DarkCaster/3DPrintingStuff/GearedExtruderDrive_V2/DriveIdler_Top/DriveIdler_Cover_625zz.FCStd

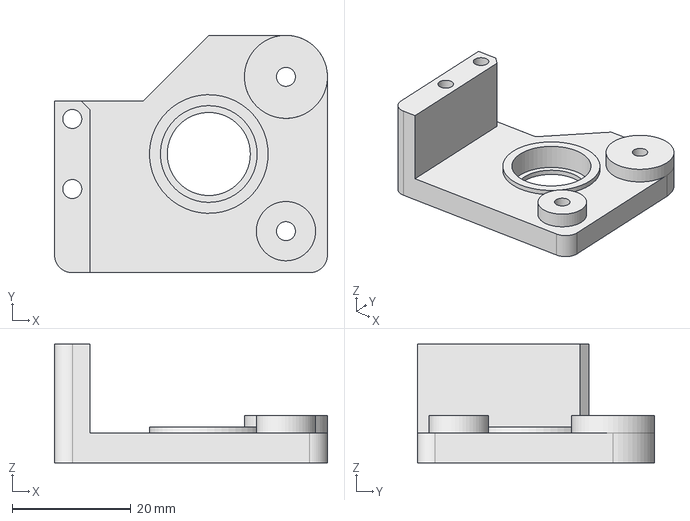
[picture p15: CAD file, 2019-01-30]
GearedExtruderDrive_V2/DriveIdler_Top/DriveIdler_Cover_625zz.FCStd
46.0 x 40.0 x 20.0 mm
