DarkCaster/3DPrintingStuff/GearedExtruderDrive_V2/Frame/FrameTop.FCStd

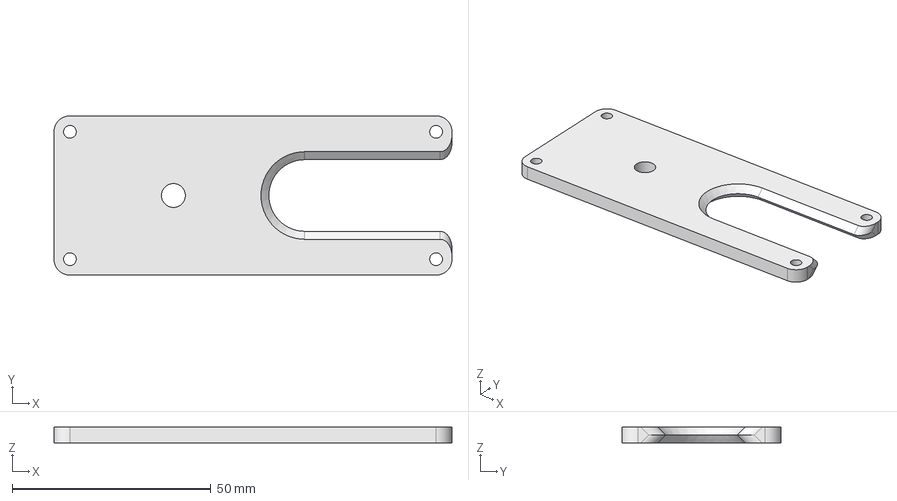
[picture p16: CAD file, 2019-02-06]
GearedExtruderDrive_V2/Frame/FrameTop.FCStd
100.0 x 40.0 x 4.00 mm
