DarkCaster/3DPrintingStuff/GearedExtruderDrive_V2/Helpers/Nema17_Motor.FCStd

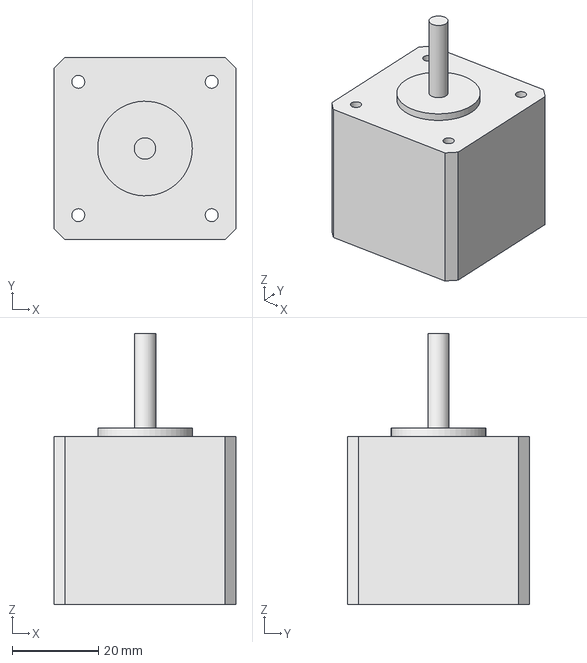
[picture p17: CAD file, 2019-01-29]
GearedExtruderDrive_V2/Helpers/Nema17_Motor.FCStd
42.3 x 42.3 x 63.0 mm
