DarkCaster/3DPrintingStuff/GearedExtruderDrive_V2/SmallGear/SmallGear_D5.4mm+M2.5.FCStd

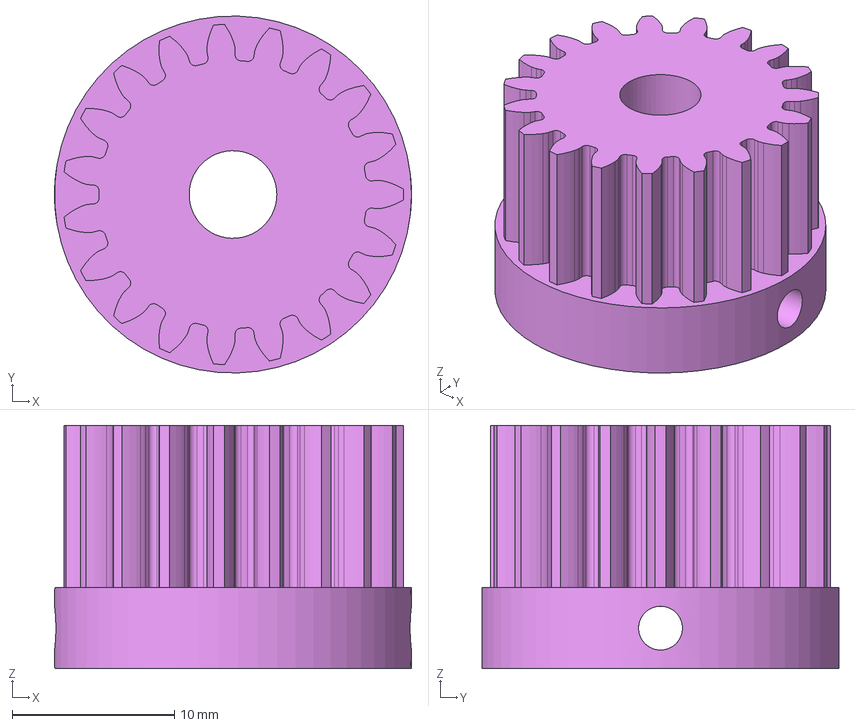
[picture p19: CAD file, 2018-07-12]
GearedExtruderDrive_V2/SmallGear/SmallGear_D5.4mm+M2.5.FCStd
22.0 x 22.0 x 15.0 mm
