DarkCaster/3DPrintingStuff/OPIRouterCase4/Bottom_Extension_Model.FCStd

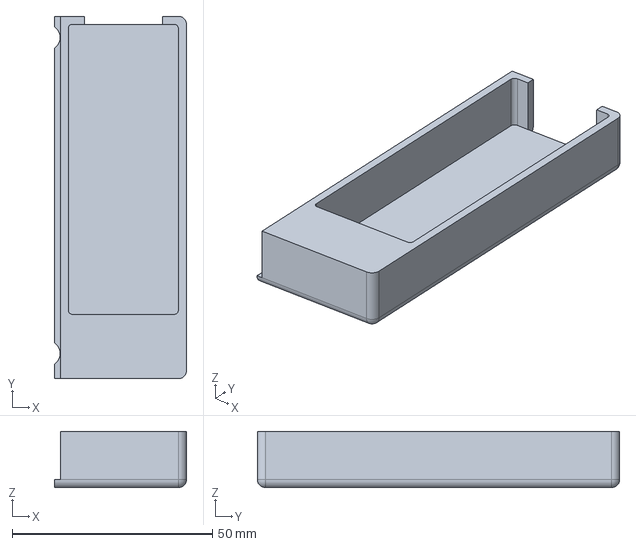
[picture p21: CAD file, 2024-11-16]
OPIRouterCase4/Bottom_Extension_Model.FCStd
33.0 x 90.6 x 14.0 mm
