DarkCaster/3DPrintingStuff/Other/StuffOrganizerV1.FCStd

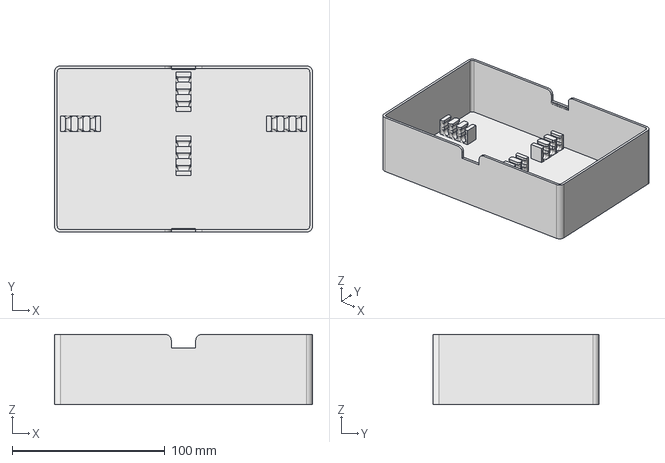
[picture p22: CAD file, 2023-09-04]
Other/StuffOrganizerV1.FCStd
169.0 x 109.0 x 46.0 mm
