DarkCaster/3DPrintingStuff/RepRap_Huxley_CustomParts/ExtruderDriveHolder/ExtruderDriveHolder4_NEMA17_Alt.FCStd

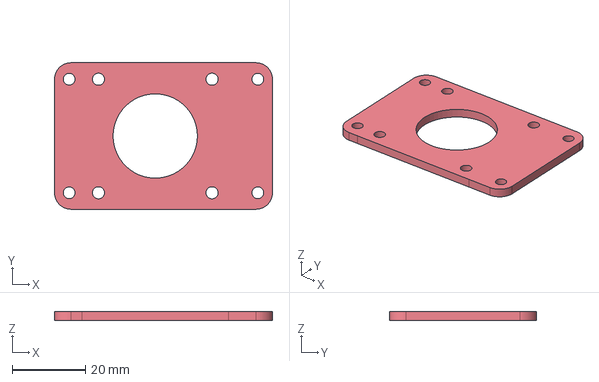
[picture p23: CAD file, 2018-10-10]
RepRap_Huxley_CustomParts/ExtruderDriveHolder/ExtruderDriveHolder4_NEMA17_Alt.FCStd
59.5 x 40.0 x 2.50 mm
