DarkCaster/3DPrintingStuff/RepRap_Huxley_CustomParts/Helpers/OpticalEndstop.FCStd

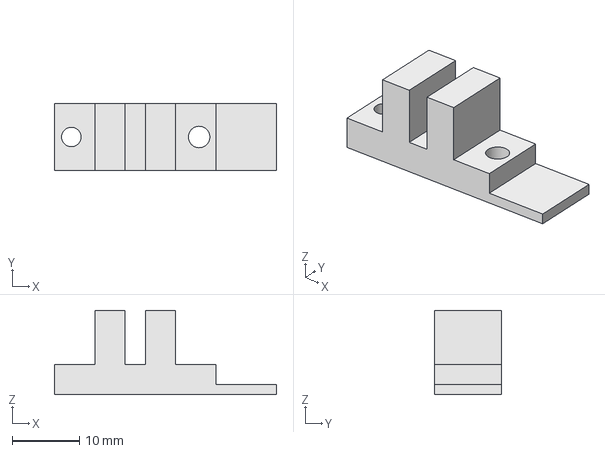
[picture p24: CAD file, 2019-01-16]
RepRap_Huxley_CustomParts/Helpers/OpticalEndstop.FCStd
33.0 x 10.0 x 12.5 mm
