DarkCaster/3DPrintingStuff/RepRap_Huxley_CustomParts/Other/LM6UU_IGUS_PETG.fcstd

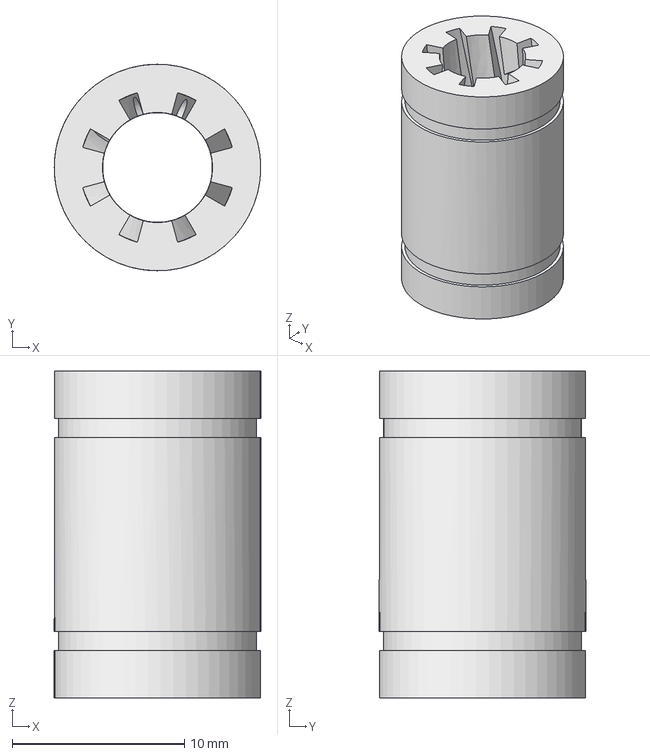
[picture p25: CAD file, 2019-02-09]
RepRap_Huxley_CustomParts/Other/LM6UU_IGUS_PETG.fcstd
12.0 x 12.0 x 19.0 mm
