DarkCaster/3DPrintingStuff/RepRap_Huxley_CustomParts/XAxis_Left/LeftXEndHalf_Top.FCStd

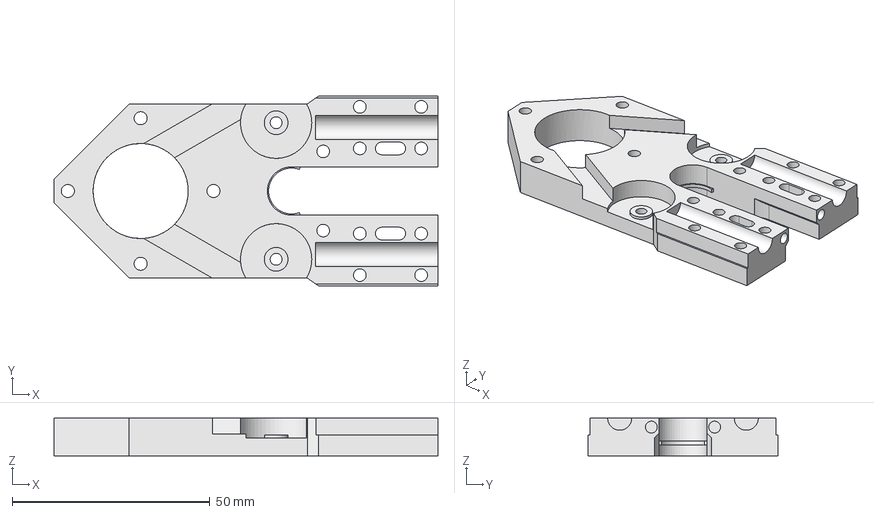
[picture p26: CAD file, 2019-01-19]
RepRap_Huxley_CustomParts/XAxis_Left/LeftXEndHalf_Top.FCStd
97.0 x 48.0 x 9.50 mm
