DarkCaster/3DPrintingStuff/RepRap_Huxley_CustomParts/XCarriage/BackTurbinePipe_TwoSides.FCStd

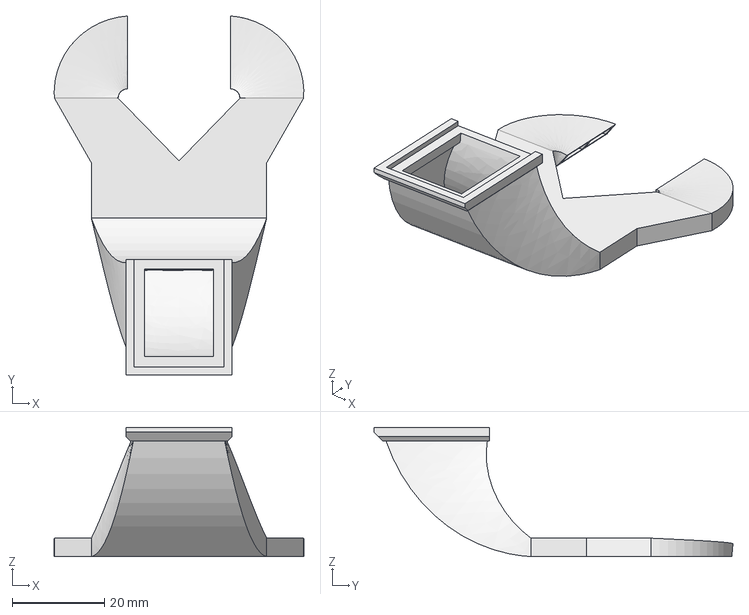
[picture p28: CAD file, 2019-01-26]
RepRap_Huxley_CustomParts/XCarriage/BackTurbinePipe_TwoSides.FCStd
54.1 x 77.8 x 28.0 mm
