DarkCaster/3DPrintingStuff/RepRap_Huxley_CustomParts/YAxis/BedClamping1_Alt2.FCStd

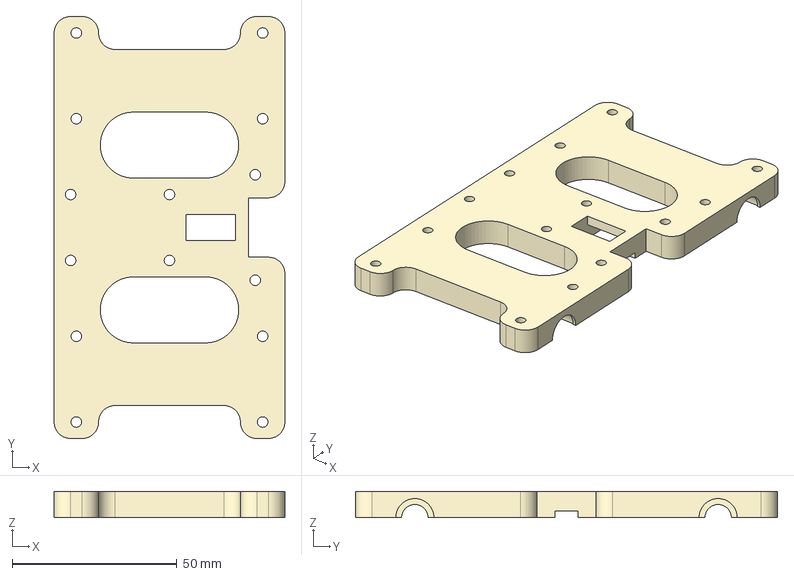
[picture p29: CAD file, 2018-10-08]
RepRap_Huxley_CustomParts/YAxis/BedClamping1_Alt2.FCStd
70.0 x 128.0 x 8.00 mm
