DarkCaster/3DPrintingStuff/RepRap_Huxley_CustomParts/ZAxis/ZThreadedRodCoupler_THSL-200-8D_D8mm.FCStd

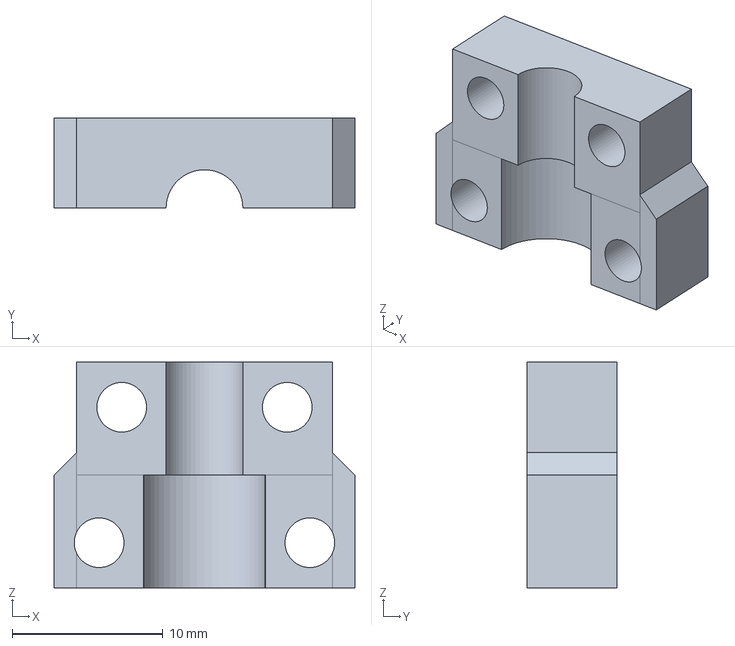
[picture p30: CAD file, 2018-09-16]
RepRap_Huxley_CustomParts/ZAxis/ZThreadedRodCoupler_THSL-200-8D_D8mm.FCStd
20.0 x 6.00 x 15.0 mm
