DarkCaster/3DPrintingStuff/Anet_E10_X_BeltLock/RightBeltLock.FCStd

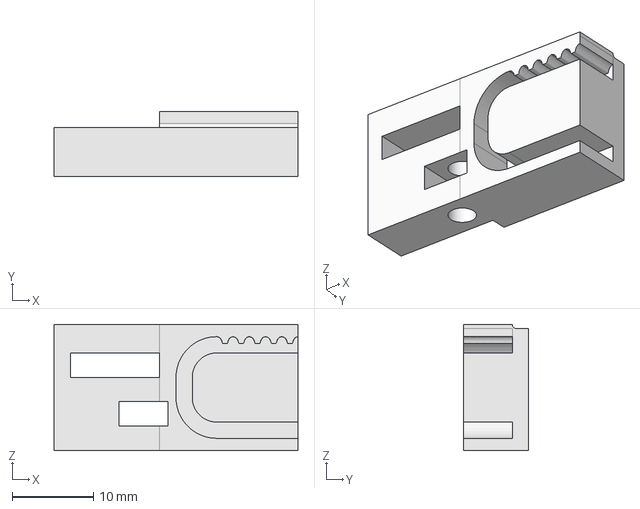
[picture p31: CAD file, 2018-05-15]
Anet_E10_X_BeltLock/RightBeltLock.FCStd
30.0 x 8.00 x 15.5 mm
