DarkCaster/3DPrintingStuff/Anet_E10_X_Carriage/XCarriage.fcstd

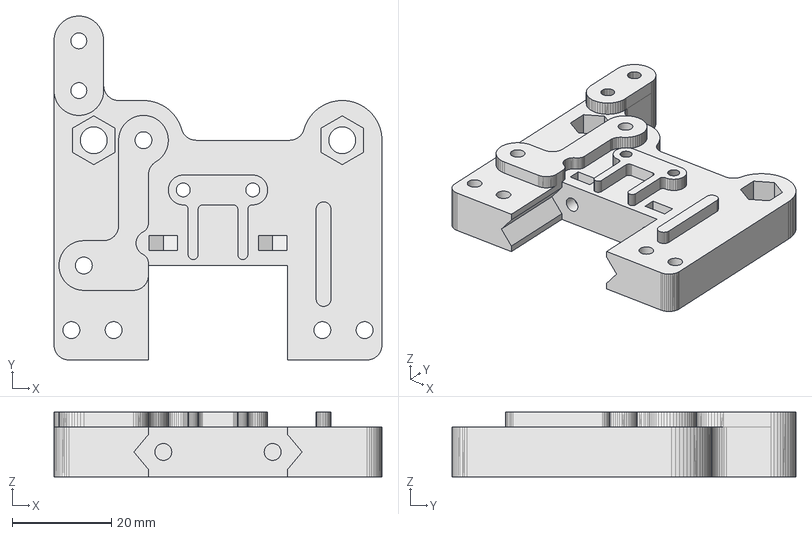
[picture p32: CAD file, 2018-11-25]
Anet_E10_X_Carriage/XCarriage.fcstd
66.0 x 69.2 x 13.0 mm
