DarkCaster/3DPrintingStuff/CalibrationSquare/VerticalSquare_Fusion.FCStd

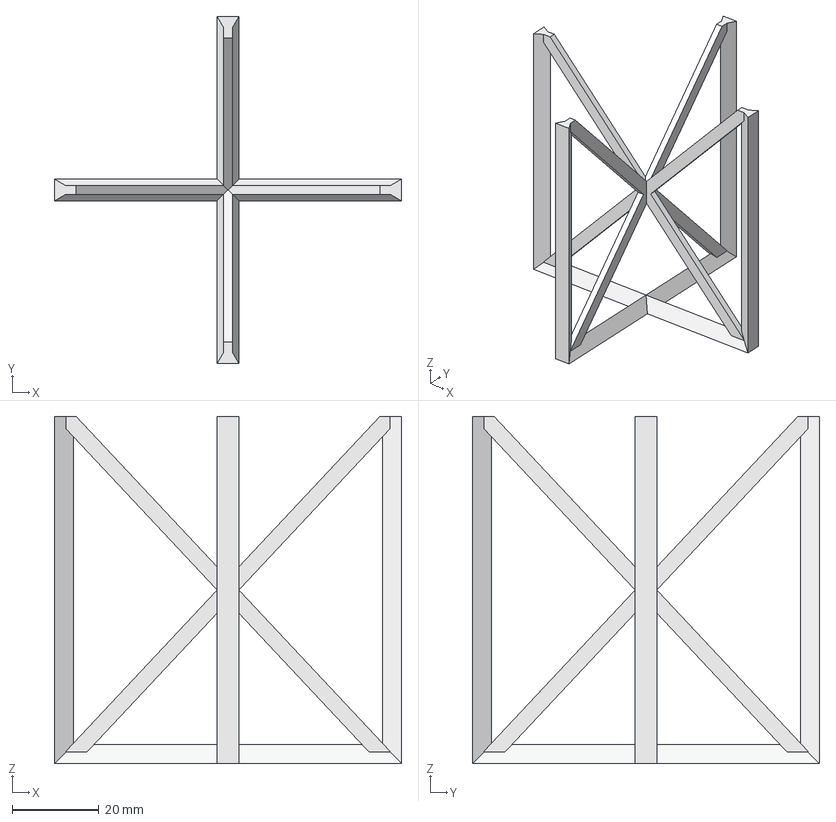
[picture p33: CAD file, 2018-10-27]
CalibrationSquare/VerticalSquare_Fusion.FCStd
80.0 x 80.0 x 80.0 mm
