DarkCaster/3DPrintingStuff/FilamentFilter/Box.FCStd

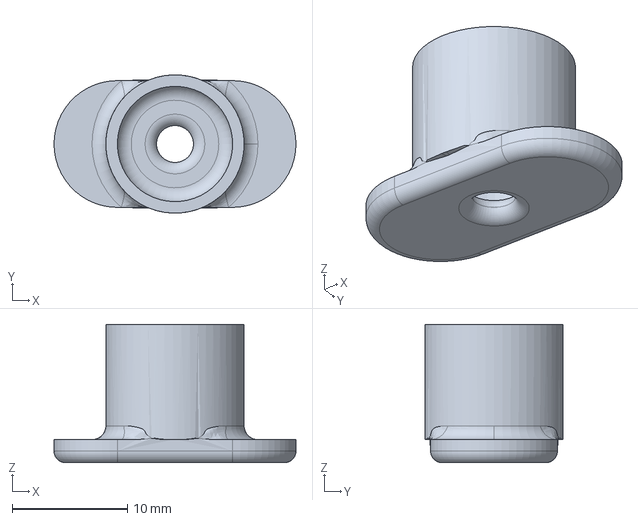
[picture p34: CAD file, 2018-07-15]
FilamentFilter/Box.FCStd
21.0 x 12.0 x 12.0 mm
