DarkCaster/3DPrintingStuff/GearedExtruderDrive_V1_NEMA17/SmallGear_V2_ABS_D5.2mm+M3.FCStd

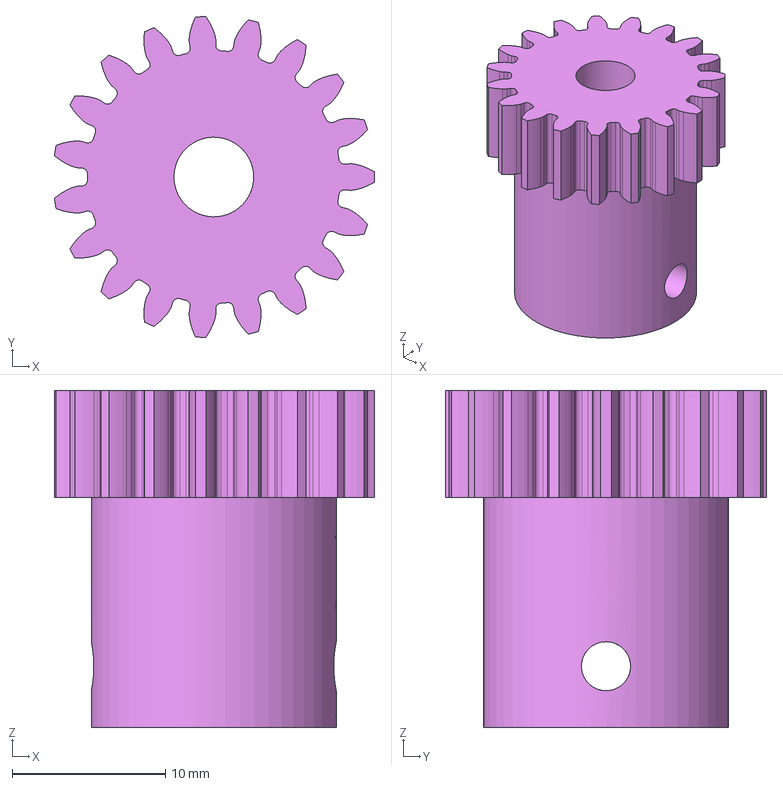
[picture p35: CAD file, 2018-07-07]
GearedExtruderDrive_V1_NEMA17/SmallGear_V2_ABS_D5.2mm+M3.FCStd
20.9 x 21.0 x 22.0 mm
