DarkCaster/3DPrintingStuff/GearedExtruderDrive_V2/DriveBase/DriveBase_Fitting_Clamp.FCStd

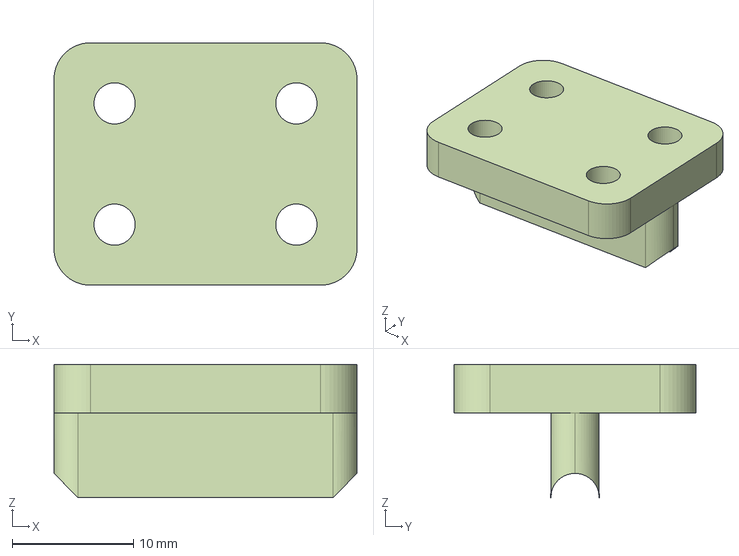
[picture p36: CAD file, 2019-02-08]
GearedExtruderDrive_V2/DriveBase/DriveBase_Fitting_Clamp.FCStd
25.0 x 20.0 x 11.0 mm
