DarkCaster/3DPrintingStuff/GearedExtruderDrive_V2/DriveIdler/DriveIdler_623zz.FCStd

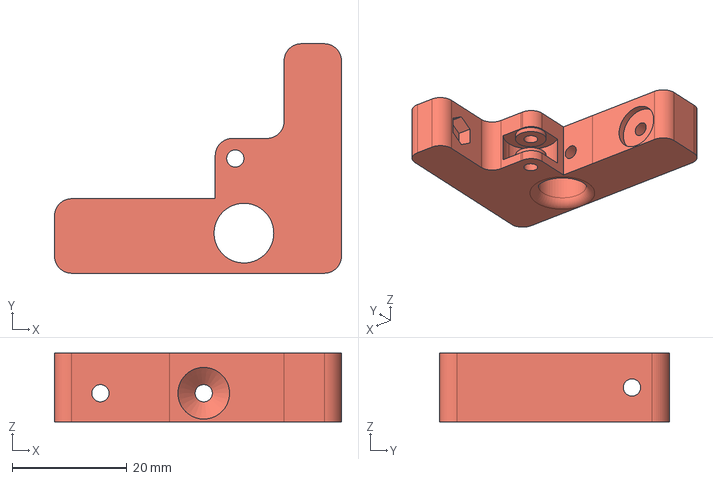
[picture p37: CAD file, 2018-07-15]
GearedExtruderDrive_V2/DriveIdler/DriveIdler_623zz.FCStd
50.0 x 40.0 x 12.0 mm
