DarkCaster/3DPrintingStuff/GearedExtruderDrive_V2/DriveIdler_Top/DriveIdlerClamp.FCStd

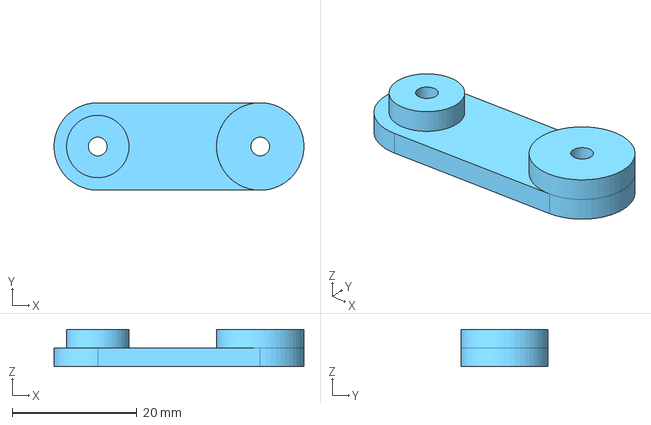
[picture p38: CAD file, 2018-07-15]
GearedExtruderDrive_V2/DriveIdler_Top/DriveIdlerClamp.FCStd
40.0 x 14.0 x 6.00 mm
