DarkCaster/3DPrintingStuff/GearedExtruderDrive_V2/LargeGearAssembly/LargeGear_M5_H8mm_ClipH4.6mm.FCStd

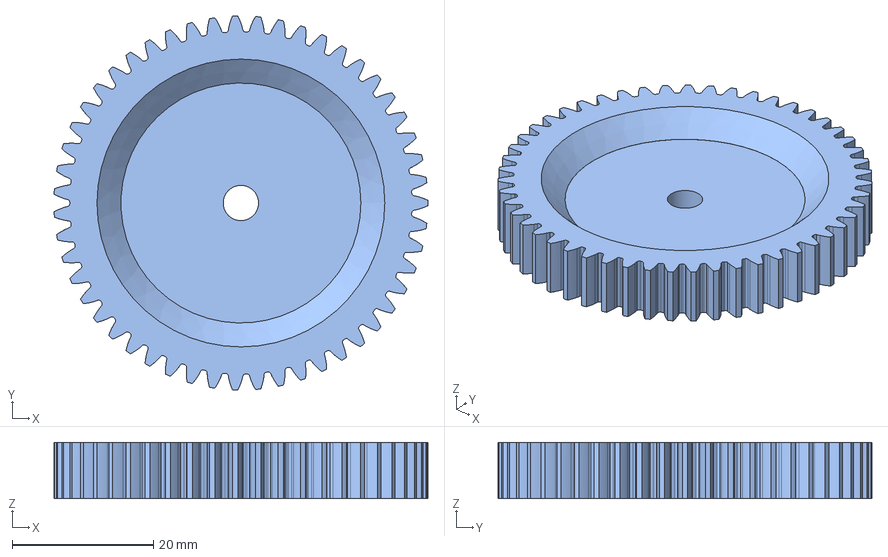
[picture p40: CAD file, 2019-02-07]
GearedExtruderDrive_V2/LargeGearAssembly/LargeGear_M5_H8mm_ClipH4.6mm.FCStd
53.0 x 53.0 x 8.00 mm
