DarkCaster/3DPrintingStuff/MiniSpool/MiniSpoolHalf2_Thick_30MM.fcstd

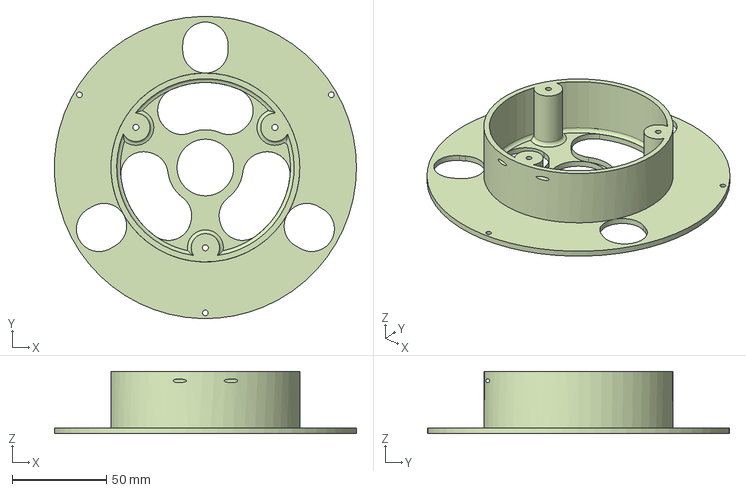
[picture p41: CAD file, 2018-12-30]
MiniSpool/MiniSpoolHalf2_Thick_30MM.fcstd
159.9 x 159.9 x 33.0 mm
