DarkCaster/3DPrintingStuff/OPIRouterCase4/Top_Case_Imported.FCStd

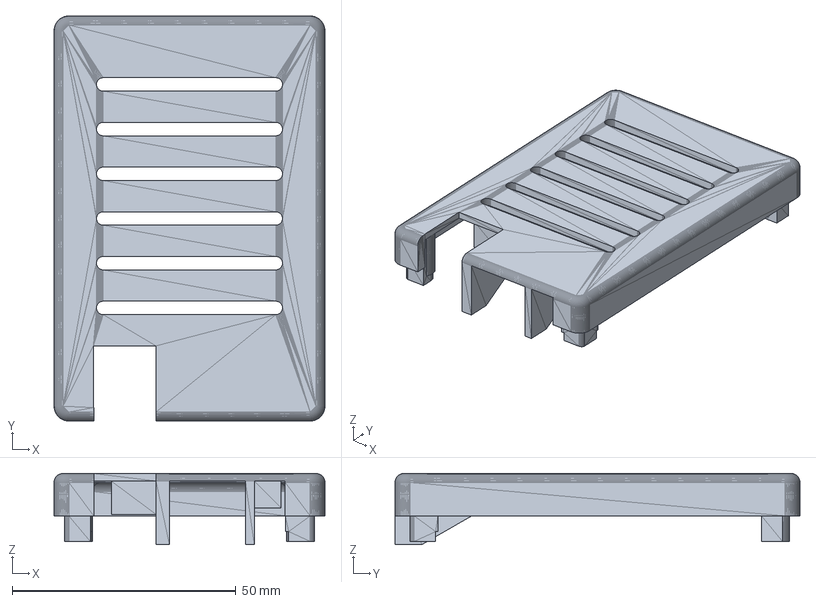
[picture p42: CAD file, 2024-11-16]
OPIRouterCase4/Top_Case_Imported.FCStd
60.6 x 90.6 x 15.9 mm
