DarkCaster/3DPrintingStuff/Other/CasePart1L.FCStd

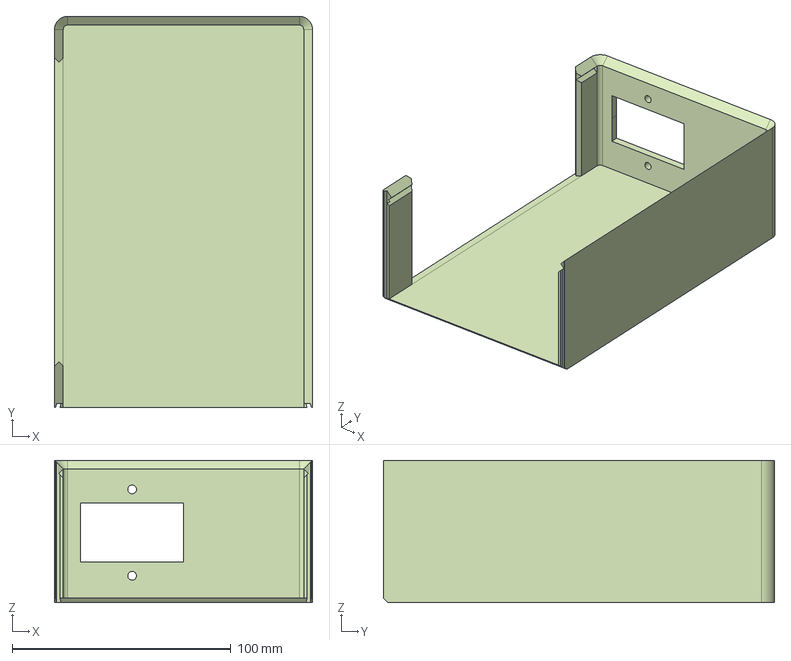
[picture p43: CAD file, 2019-06-28]
Other/CasePart1L.FCStd
118.0 x 179.0 x 65.0 mm
