DarkCaster/3DPrintingStuff/RepRap_Huxley_CustomParts/ExtruderDriveHolder/ExtruderDriveHolder1_Alt.FCStd

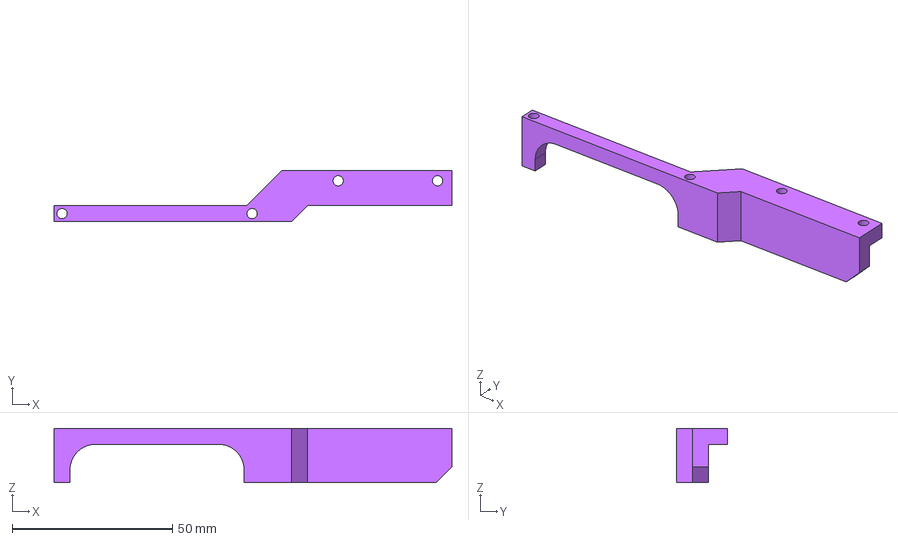
[picture p45: CAD file, 2018-10-10]
RepRap_Huxley_CustomParts/ExtruderDriveHolder/ExtruderDriveHolder1_Alt.FCStd
124.2 x 16.0 x 17.0 mm
