DarkCaster/3DPrintingStuff/RepRap_Huxley_CustomParts/Helpers/Rod_M6x365mm.FCStd

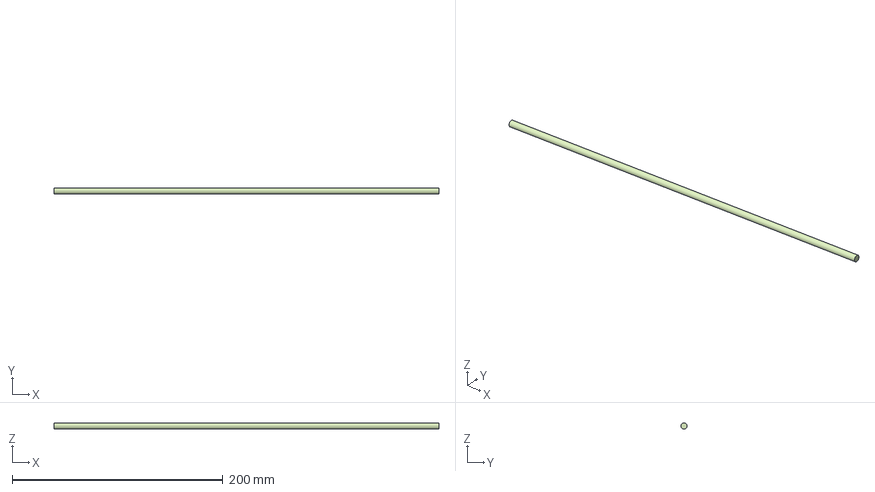
[picture p46: CAD file, 2019-01-15]
RepRap_Huxley_CustomParts/Helpers/Rod_M6x365mm.FCStd
365.0 x 5.99 x 6.00 mm
