DarkCaster/3DPrintingStuff/RepRap_Huxley_CustomParts/XAxis_Right/RightXEndHalf_Top.FCStd

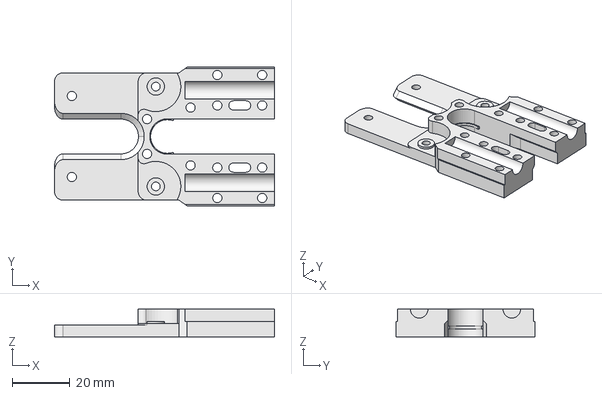
[picture p47: CAD file, 2019-01-19]
RepRap_Huxley_CustomParts/XAxis_Right/RightXEndHalf_Top.FCStd
76.0 x 48.0 x 9.50 mm
