DarkCaster/3DPrintingStuff/RepRap_Huxley_CustomParts/XCarriage/CarriageHalf_Top.FCStd

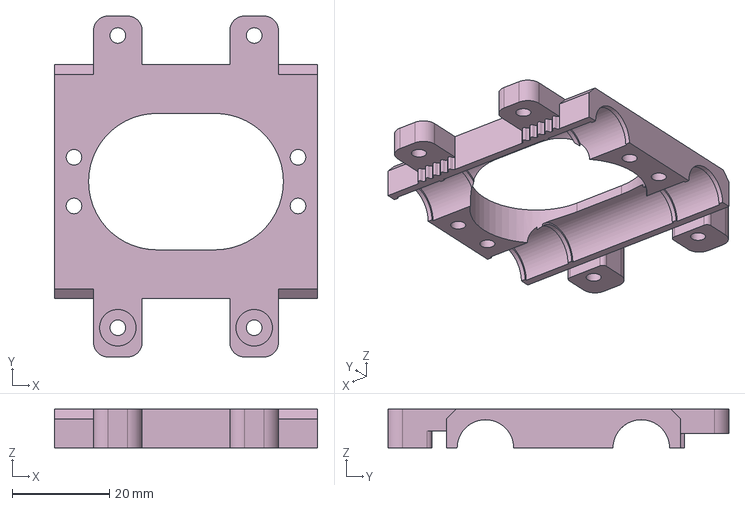
[picture p48: CAD file, 2019-01-17]
RepRap_Huxley_CustomParts/XCarriage/CarriageHalf_Top.FCStd
54.0 x 70.0 x 8.00 mm
