DarkCaster/3DPrintingStuff/RepRap_Huxley_CustomParts/YAxis/BedClamping2_Alt2.FCStd

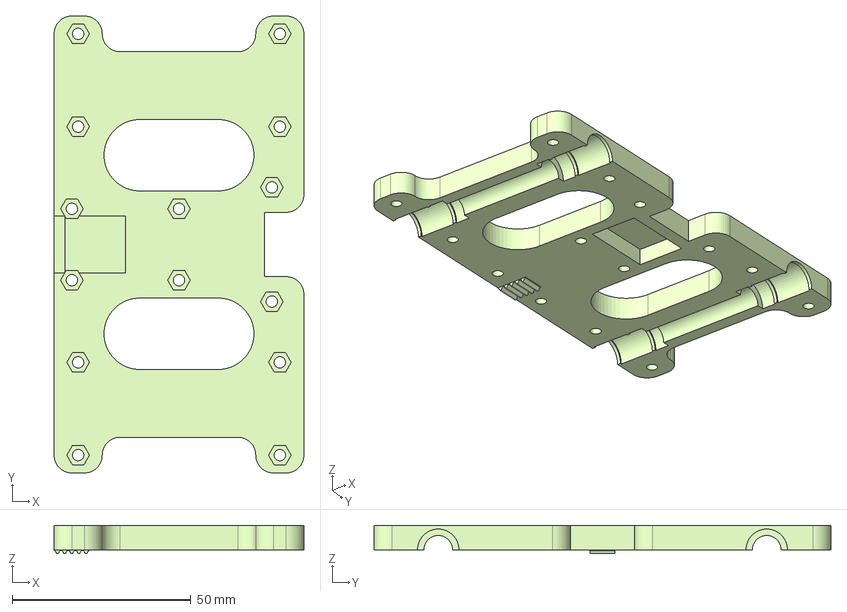
[picture p49: CAD file, 2018-10-08]
RepRap_Huxley_CustomParts/YAxis/BedClamping2_Alt2.FCStd
70.0 x 128.0 x 7.85 mm
