DarkCaster/3DPrintingStuff/RepRap_Huxley_CustomParts/ZAxis/ZThreadedRodCoupler_M5.FCStd

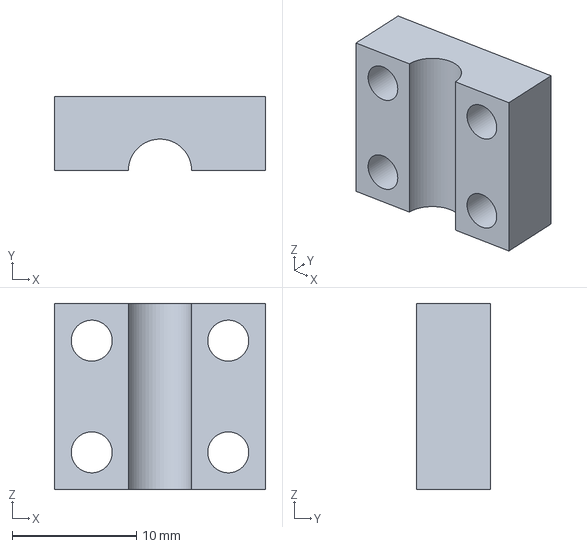
[picture p50: CAD file, 2018-09-03]
RepRap_Huxley_CustomParts/ZAxis/ZThreadedRodCoupler_M5.FCStd
17.0 x 6.00 x 15.0 mm
