DarkCaster/3DPrintingStuff/CalibrationSquare/VerticalSquare.FCStd

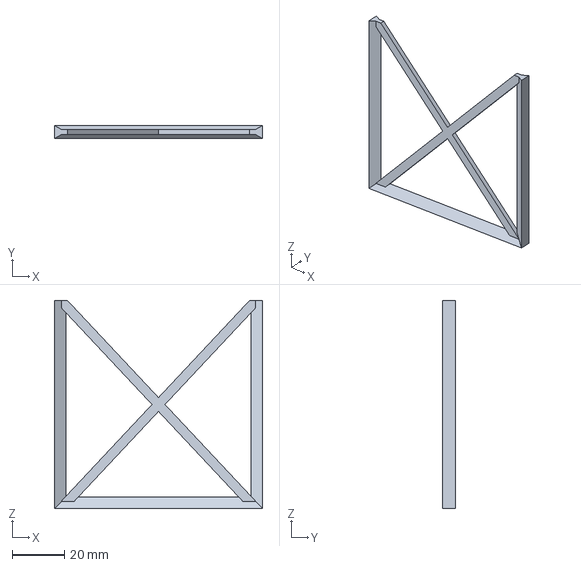
[picture p51: CAD file, 2018-07-15]
CalibrationSquare/VerticalSquare.FCStd
80.0 x 5.00 x 80.0 mm
