DarkCaster/3DPrintingStuff/GearedExtruderDrive_V2/DriveBase/DriveBase_Tight.FCStd

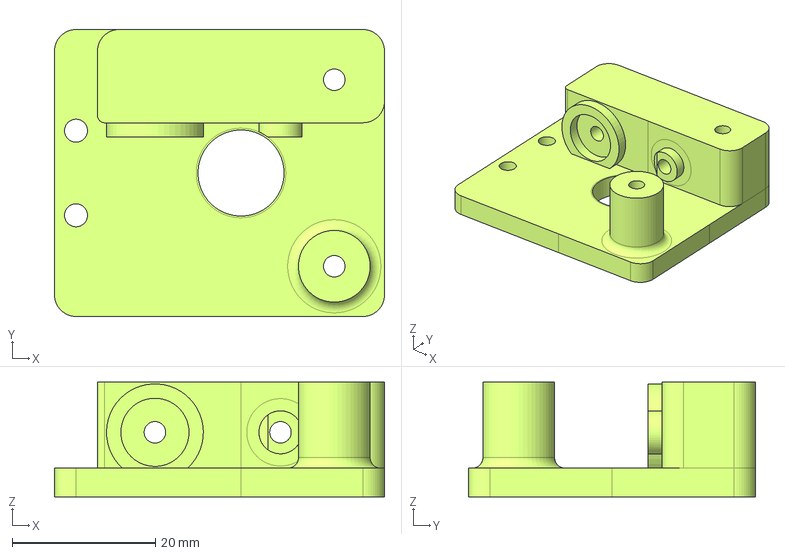
[picture p52: CAD file, 2018-10-31]
GearedExtruderDrive_V2/DriveBase/DriveBase_Tight.FCStd
46.0 x 40.0 x 16.0 mm
