DarkCaster/3DPrintingStuff/GearedExtruderDrive_V2/Frame/FrontStand_H20.5mm.FCStd

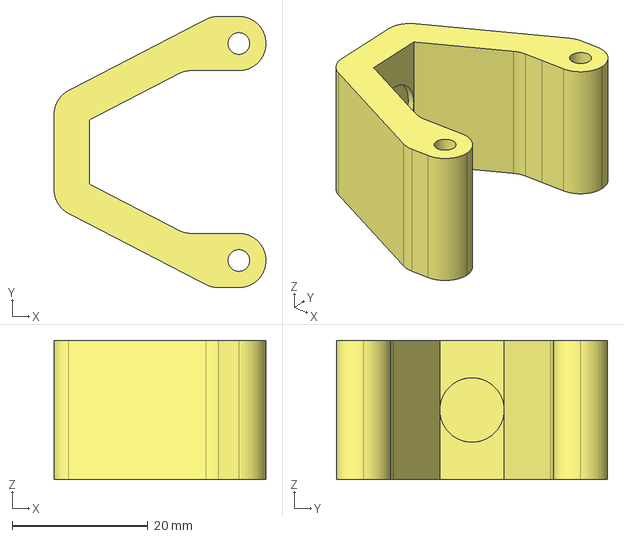
[picture p53: CAD file, 2018-07-12]
GearedExtruderDrive_V2/Frame/FrontStand_H20.5mm.FCStd
31.3 x 40.0 x 20.5 mm
