DarkCaster/3DPrintingStuff/GearedExtruderDrive_V2/LargeGearAssembly/IdlerPart_625zz.FCStd

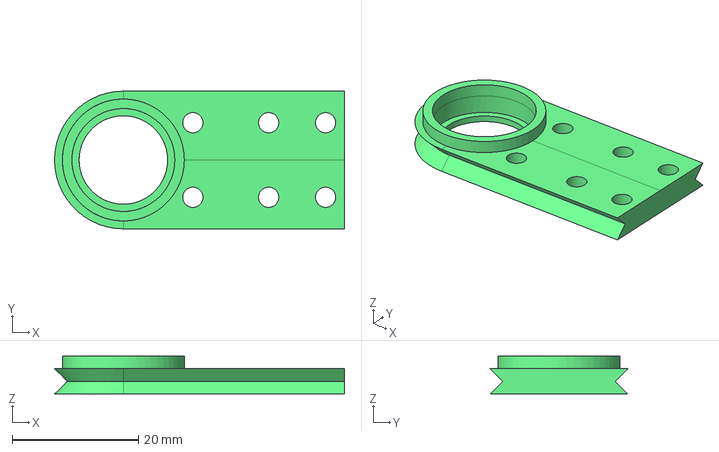
[picture p54: CAD file, 2018-07-12]
GearedExtruderDrive_V2/LargeGearAssembly/IdlerPart_625zz.FCStd
45.9 x 21.8 x 6.00 mm
