DarkCaster/3DPrintingStuff/MiniSpool/MiniSpoolHalf_Thick_15MM.fcstd

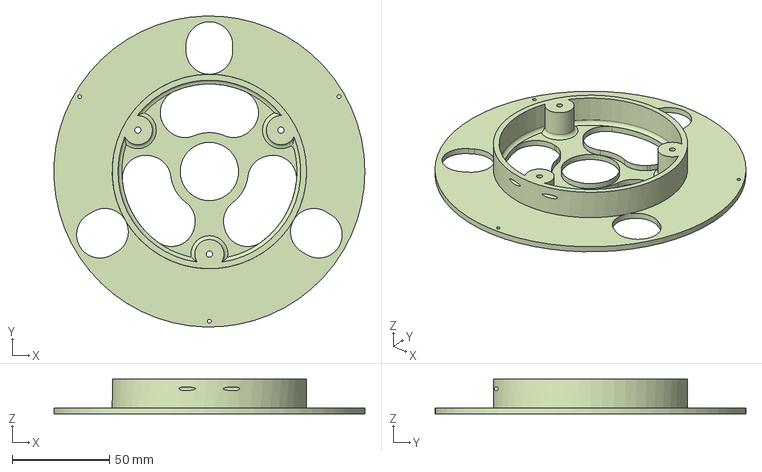
[picture p55: CAD file, 2018-11-22]
MiniSpool/MiniSpoolHalf_Thick_15MM.fcstd
159.9 x 159.9 x 18.0 mm
