DarkCaster/3DPrintingStuff/OPIRouterCase4/Bottom_Case_Imported.FCStd

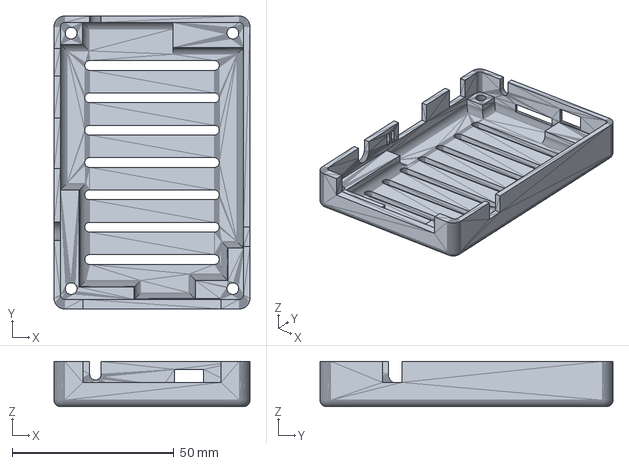
[picture p56: CAD file, 2024-11-16]
OPIRouterCase4/Bottom_Case_Imported.FCStd
60.6 x 90.6 x 14.0 mm
