DarkCaster/3DPrintingStuff/Other/ZTEBatteryPowerAdapter.fcstd

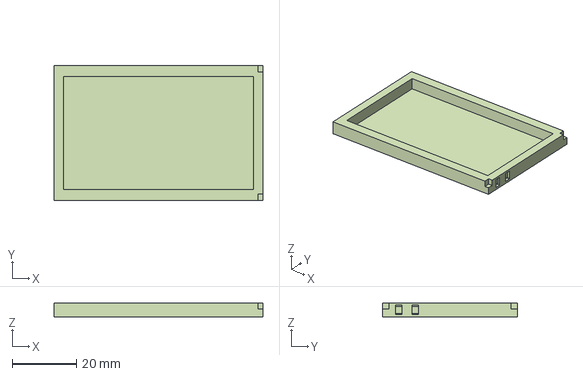
[picture p57: CAD file, 2018-11-06]
Other/ZTEBatteryPowerAdapter.fcstd
65.0 x 42.0 x 4.50 mm
