DarkCaster/3DPrintingStuff/RepRap_Huxley_CustomParts/BedRodsAlignmentToolHalf.FCStd

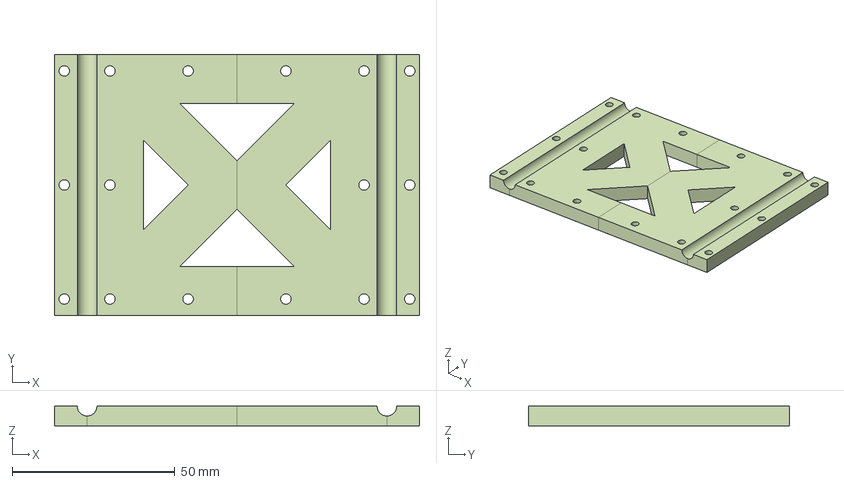
[picture p58: CAD file, 2018-10-02]
RepRap_Huxley_CustomParts/BedRodsAlignmentToolHalf.FCStd
112.0 x 80.0 x 6.00 mm
