DarkCaster/3DPrintingStuff/RepRap_Huxley_CustomParts/ExtruderDriveHolder/ExtruderDriveHolder_Clip.FCStd

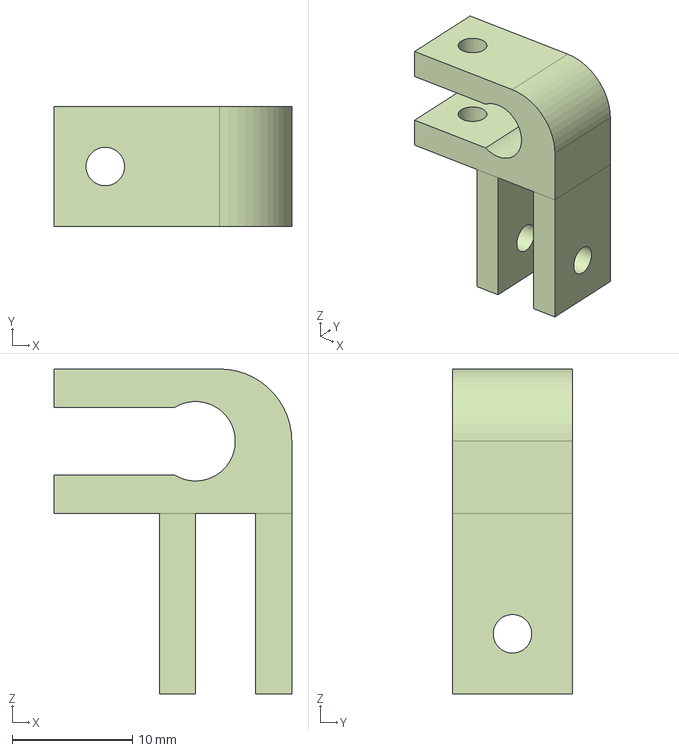
[picture p59: CAD file, 2018-10-10]
RepRap_Huxley_CustomParts/ExtruderDriveHolder/ExtruderDriveHolder_Clip.FCStd
19.7 x 10.0 x 27.0 mm
