DarkCaster/3DPrintingStuff/RepRap_Huxley_CustomParts/Helpers/Huxley_TopFrameVertex.FCStd

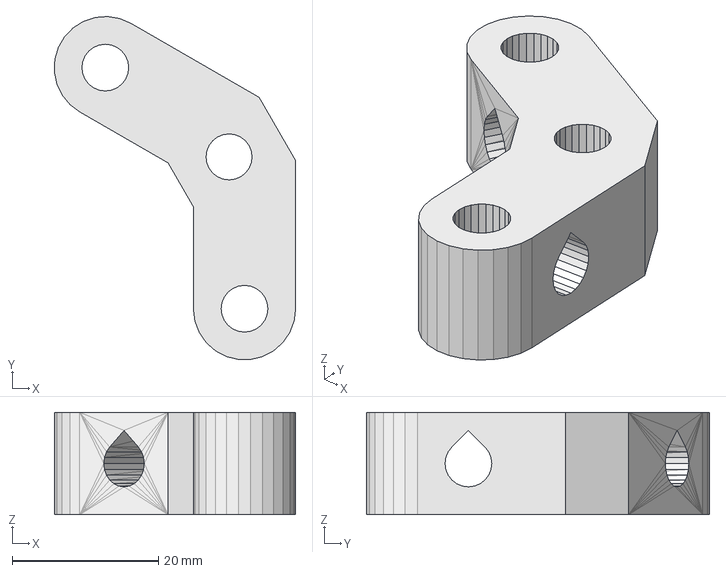
[picture p60: CAD file, 2019-01-15]
RepRap_Huxley_CustomParts/Helpers/Huxley_TopFrameVertex.FCStd
33.0 x 46.9 x 14.0 mm
