DarkCaster/3DPrintingStuff/RepRap_Huxley_CustomParts/XAxis_Left/BearingClamp.FCStd

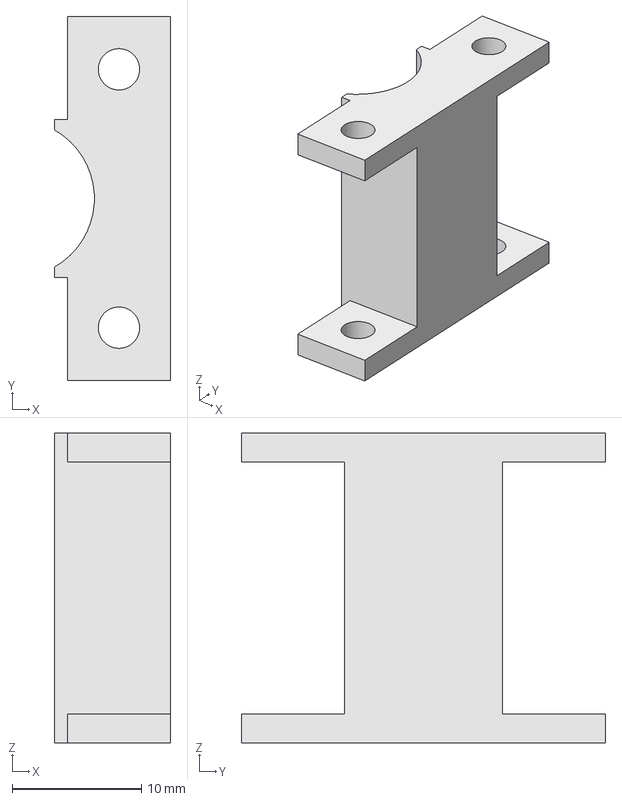
[picture p61: CAD file, 2019-01-19]
RepRap_Huxley_CustomParts/XAxis_Left/BearingClamp.FCStd
9.00 x 28.2 x 24.0 mm
