DarkCaster/3DPrintingStuff/RepRap_Huxley_CustomParts/XAxis_Right/ZEndstopClip2.FCStd

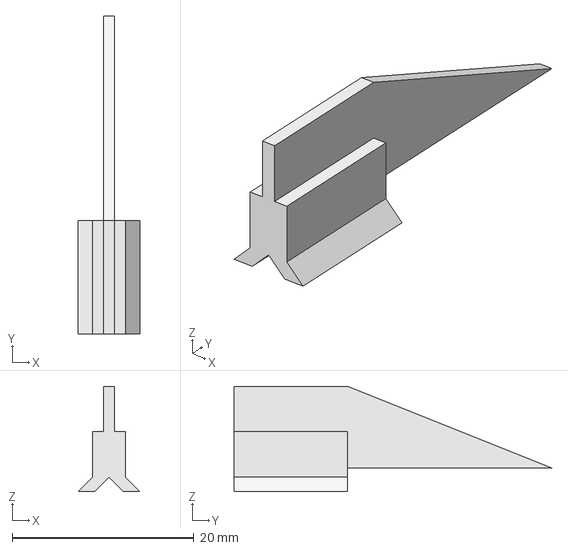
[picture p62: CAD file, 2019-01-16]
RepRap_Huxley_CustomParts/XAxis_Right/ZEndstopClip2.FCStd
6.80 x 35.0 x 11.6 mm
