DarkCaster/3DPrintingStuff/RepRap_Huxley_CustomParts/XCarriage/BackTurbineClip.FCStd

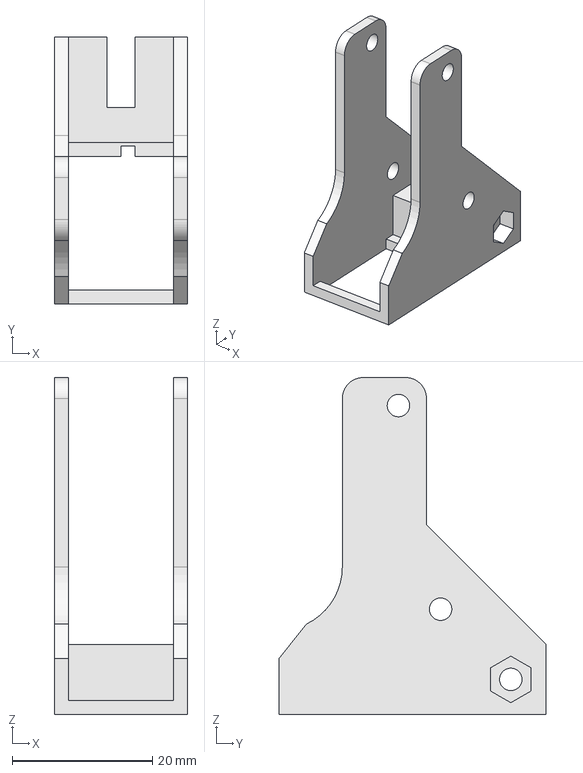
[picture p63: CAD file, 2019-01-12]
RepRap_Huxley_CustomParts/XCarriage/BackTurbineClip.FCStd
19.0 x 38.0 x 48.0 mm
