DarkCaster/3DPrintingStuff/RepRap_Huxley_CustomParts/YAxis/BedClamping3_Alt2.FCStd

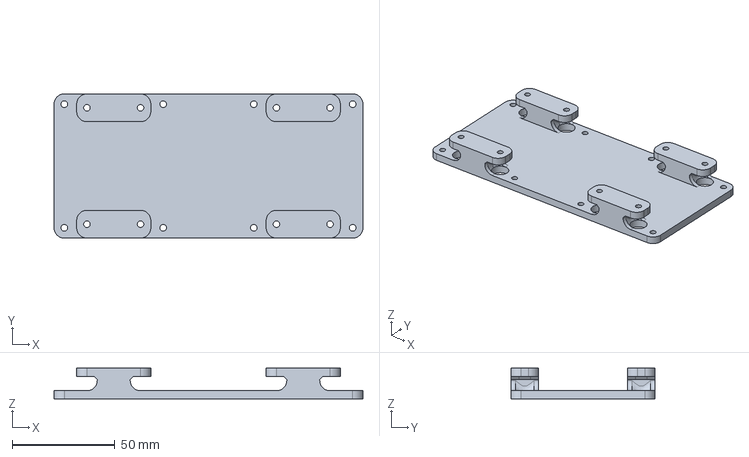
[picture p64: CAD file, 2018-10-05]
RepRap_Huxley_CustomParts/YAxis/BedClamping3_Alt2.FCStd
150.0 x 70.0 x 15.0 mm
