DarkCaster/3DPrintingStuff/RepRap_Huxley_CustomParts/ZAxis/ZEndStopClip.FCStd

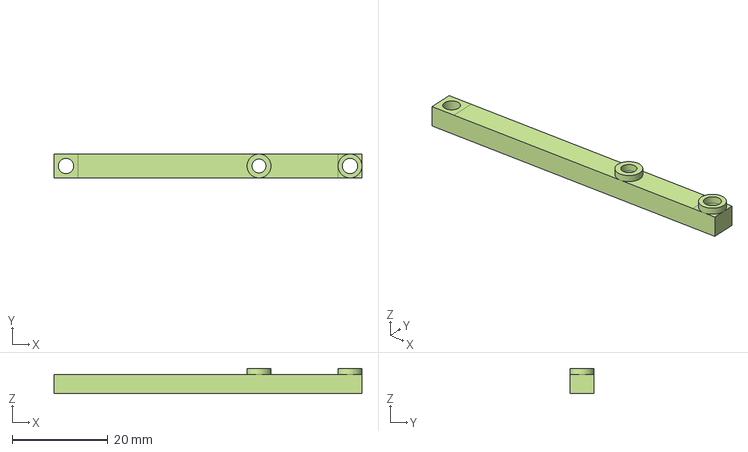
[picture p65: CAD file, 2018-08-24]
RepRap_Huxley_CustomParts/ZAxis/ZEndStopClip.FCStd
64.3 x 5.00 x 5.25 mm
