DarkCaster/3DPrintingStuff/GearedExtruderDrive_V2/DriveBase/DriveBase.FCStd

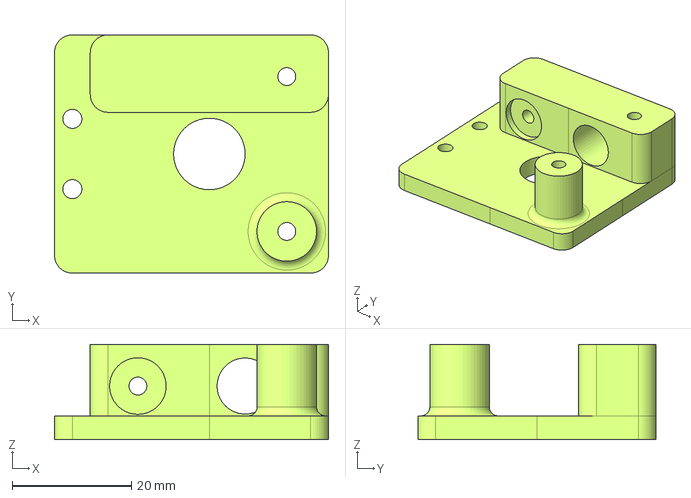
[picture p66: CAD file, 2018-07-14]
GearedExtruderDrive_V2/DriveBase/DriveBase.FCStd
46.0 x 40.0 x 16.0 mm
