DarkCaster/3DPrintingStuff/GearedExtruderDrive_V2/Frame/BackStand_H20.5mm.FCStd

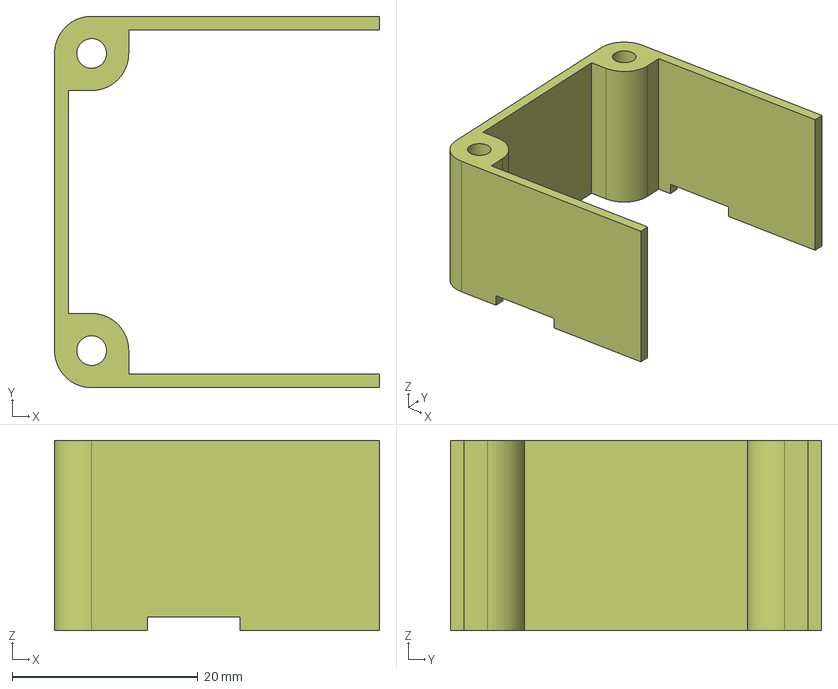
[picture p67: CAD file, 2018-07-11]
GearedExtruderDrive_V2/Frame/BackStand_H20.5mm.FCStd
35.0 x 40.0 x 20.5 mm
