DarkCaster/3DPrintingStuff/GearedExtruderDrive_V2/LargeGearAssembly/IdlerStand_H20.5mm.FCStd

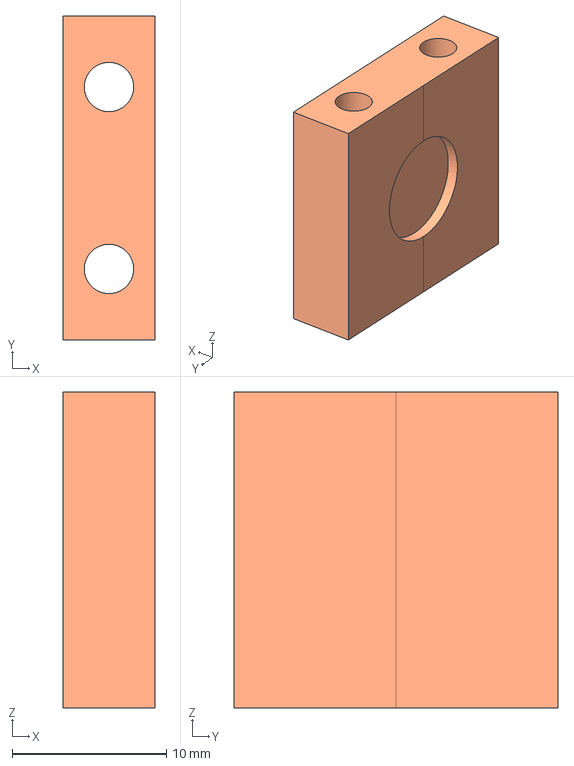
[picture p68: CAD file, 2018-07-12]
GearedExtruderDrive_V2/LargeGearAssembly/IdlerStand_H20.5mm.FCStd
6.00 x 21.0 x 20.5 mm
