DarkCaster/3DPrintingStuff/OPIRouterCase4/Top_Extension_Model.FCStd

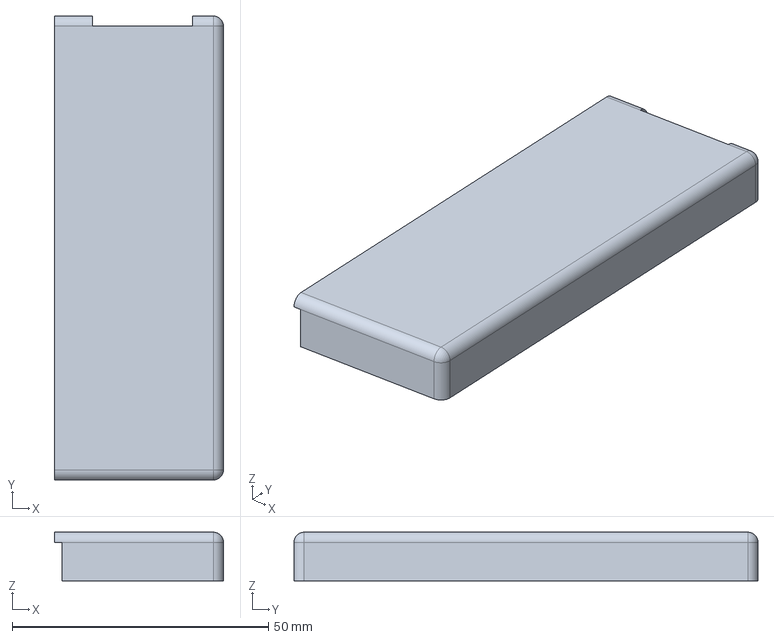
[picture p70: CAD file, 2024-11-16]
OPIRouterCase4/Top_Extension_Model.FCStd
33.0 x 90.6 x 9.50 mm
