DarkCaster/3DPrintingStuff/Other/IECSocketClip.FCStd

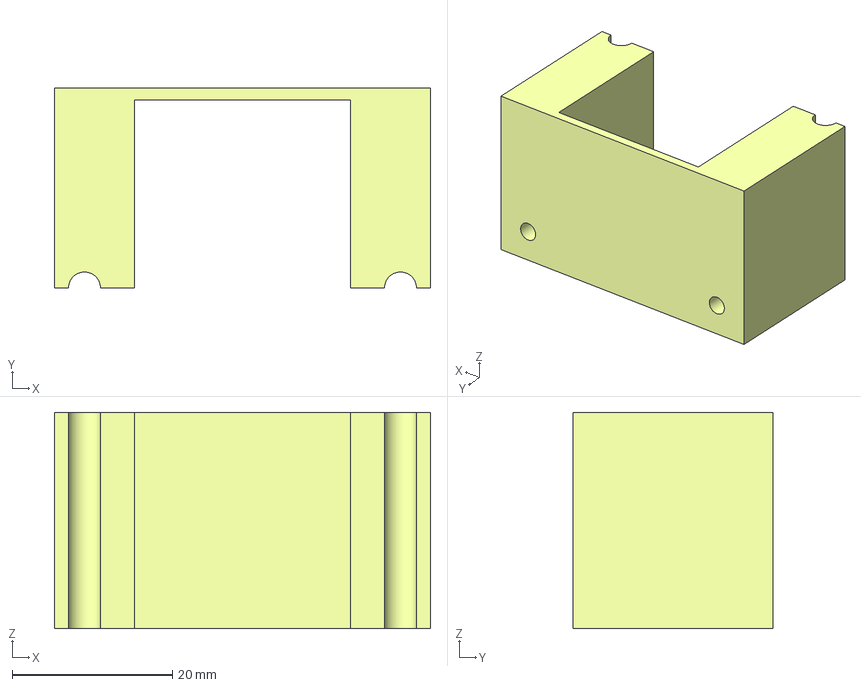
[picture p71: CAD file, 2018-09-25]
Other/IECSocketClip.FCStd
47.0 x 25.0 x 27.0 mm
