DarkCaster/3DPrintingStuff/RepRap_Huxley_CustomParts/ExtruderDriveHolder/ExtruderDriveHolder3_Alt.FCStd

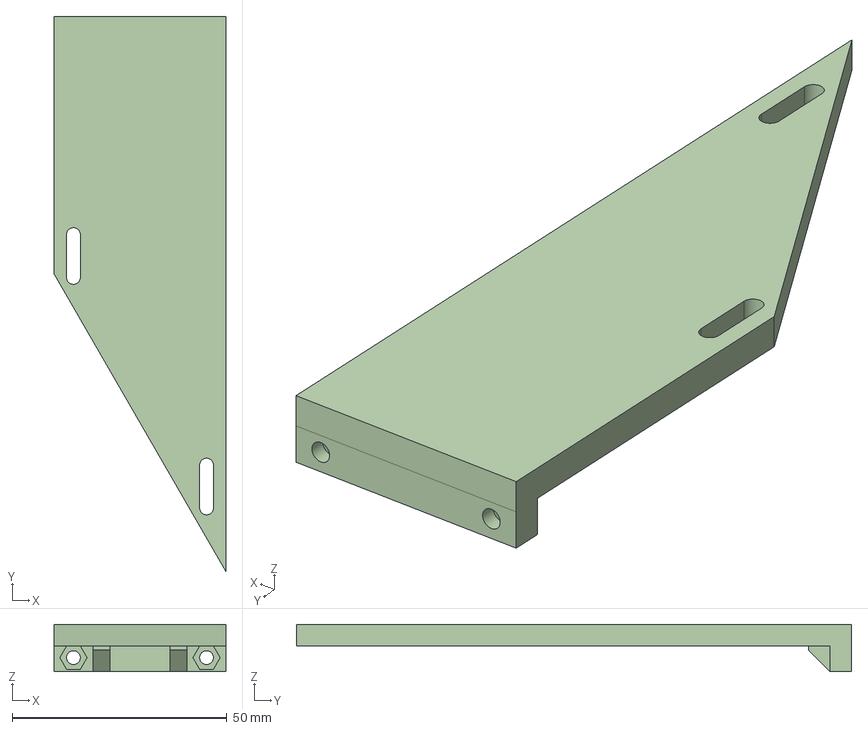
[picture p72: CAD file, 2018-10-09]
RepRap_Huxley_CustomParts/ExtruderDriveHolder/ExtruderDriveHolder3_Alt.FCStd
40.0 x 129.3 x 11.0 mm
