DarkCaster/3DPrintingStuff/RepRap_Huxley_CustomParts/Other/LM6UU_IGUS.fcstd

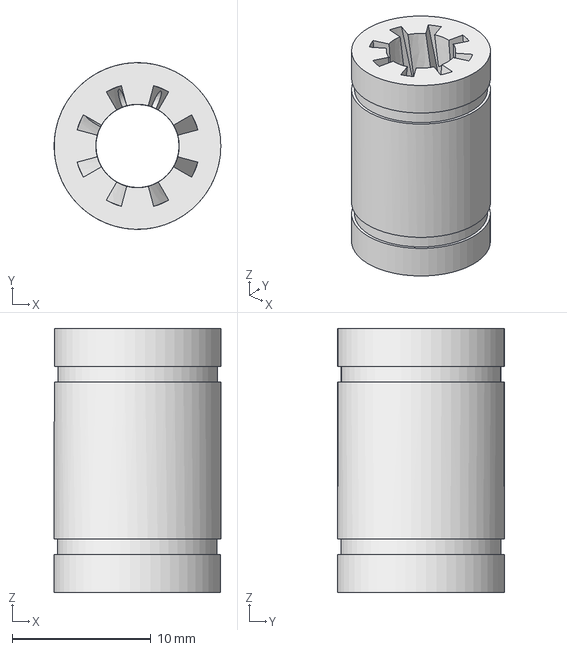
[picture p74: CAD file, 2018-12-19]
RepRap_Huxley_CustomParts/Other/LM6UU_IGUS.fcstd
12.0 x 12.0 x 19.0 mm
