DarkCaster/3DPrintingStuff/RepRap_Huxley_CustomParts/XAxis_Left/XEndstopClip1.FCStd

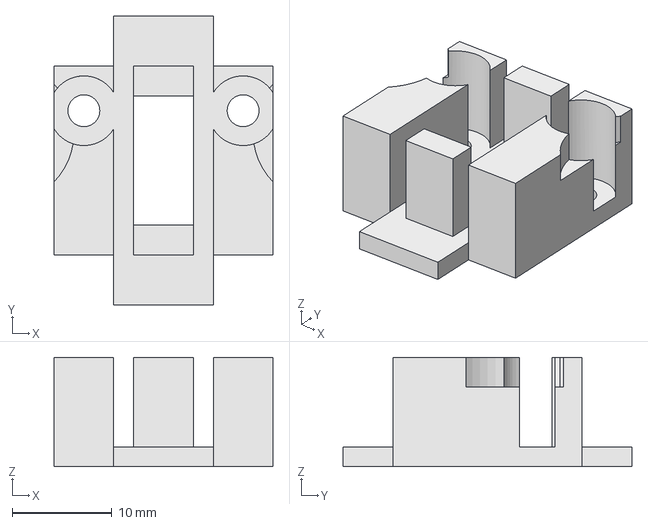
[picture p75: CAD file, 2019-01-17]
RepRap_Huxley_CustomParts/XAxis_Left/XEndstopClip1.FCStd
22.0 x 29.0 x 11.0 mm
