DarkCaster/3DPrintingStuff/RepRap_Huxley_CustomParts/XAxis_Right/ZEndstopClip1.FCStd

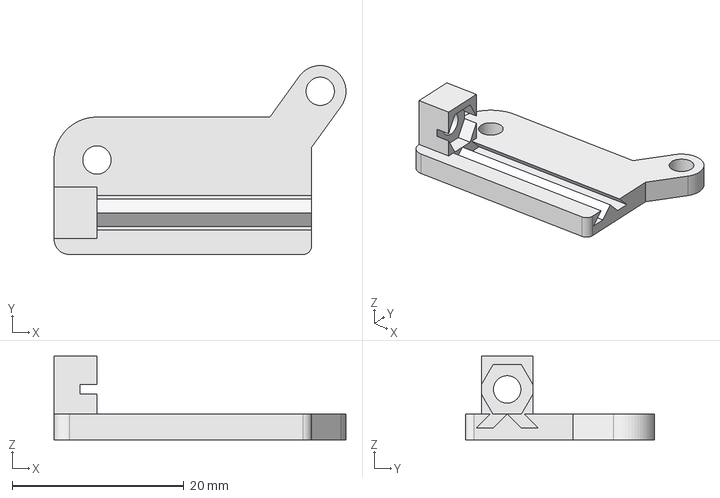
[picture p76: CAD file, 2019-01-16]
RepRap_Huxley_CustomParts/XAxis_Right/ZEndstopClip1.FCStd
34.0 x 22.0 x 9.75 mm
