DarkCaster/3DPrintingStuff/RepRap_Huxley_CustomParts/XCarriage/BackTurbinePipe_Direct.FCStd

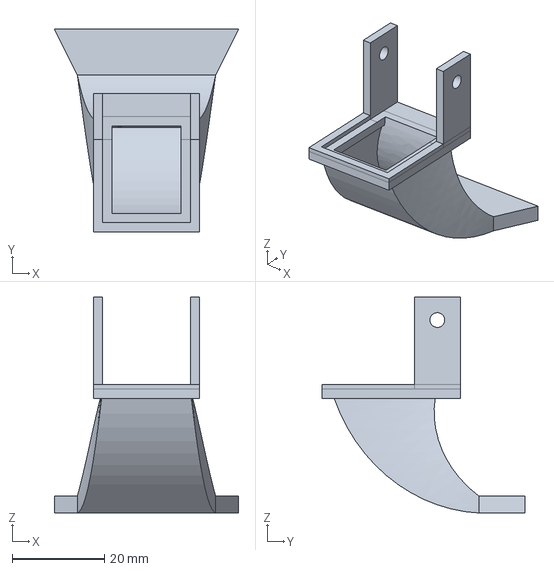
[picture p77: CAD file, 2019-01-12]
RepRap_Huxley_CustomParts/XCarriage/BackTurbinePipe_Direct.FCStd
40.0 x 44.0 x 46.9 mm
