DarkCaster/3DPrintingStuff/RepRap_Huxley_CustomParts/YAxis/BedBeltClamp3_Alt2.FCStd

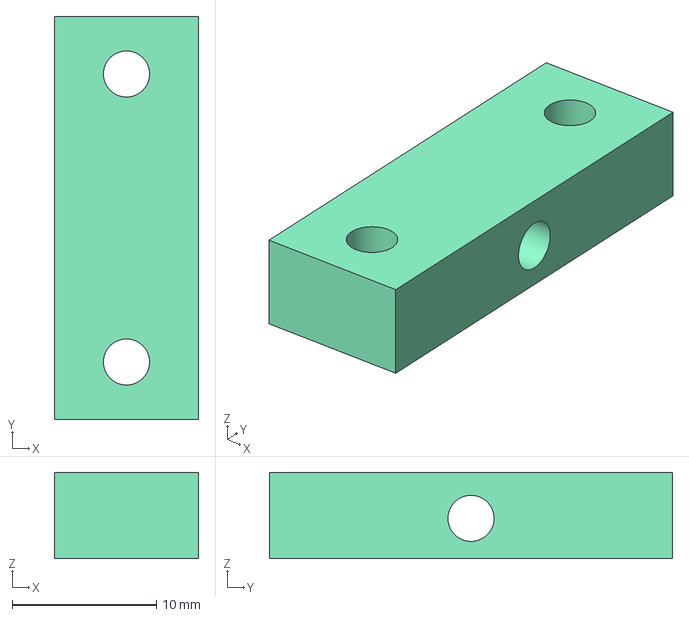
[picture p78: CAD file, 2018-10-04]
RepRap_Huxley_CustomParts/YAxis/BedBeltClamp3_Alt2.FCStd
10.0 x 28.0 x 6.00 mm
