DarkCaster/3DPrintingStuff/RepRap_Huxley_CustomParts/ZAxis/ZEndStopClip2.FCStd

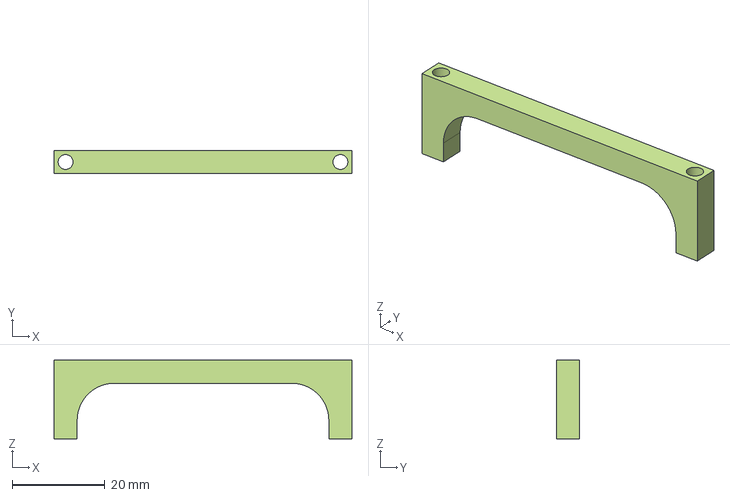
[picture p79: CAD file, 2018-08-24]
RepRap_Huxley_CustomParts/ZAxis/ZEndStopClip2.FCStd
64.3 x 5.00 x 17.0 mm
