DarkCaster/3DPrintingStuff/GearedExtruderDrive_V1_NEMA17/SmallGear_V1_ABS_D5mm+M3.FCStd

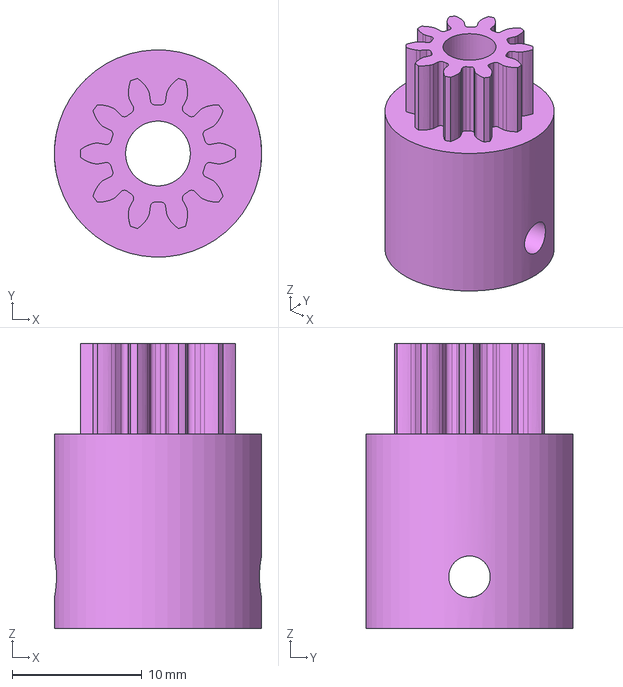
[picture p80: CAD file, 2018-06-14]
GearedExtruderDrive_V1_NEMA17/SmallGear_V1_ABS_D5mm+M3.FCStd
16.0 x 16.0 x 22.0 mm
