DarkCaster/3DPrintingStuff/GearedExtruderDrive_V2/Frame/NEMA17Spacer.FCStd

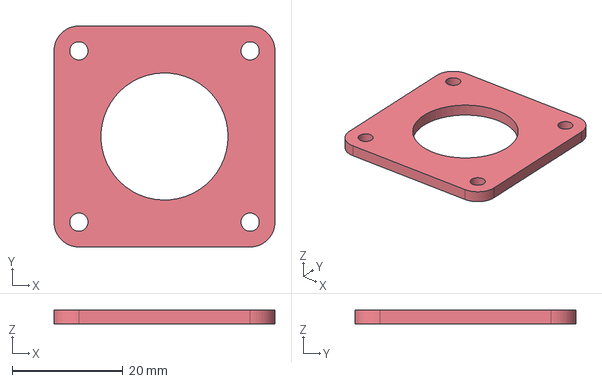
[picture p81: CAD file, 2018-07-09]
GearedExtruderDrive_V2/Frame/NEMA17Spacer.FCStd
40.0 x 40.0 x 2.50 mm
