DarkCaster/3DPrintingStuff/MiniSpool/MiniSpoolHalf2_15MM.fcstd

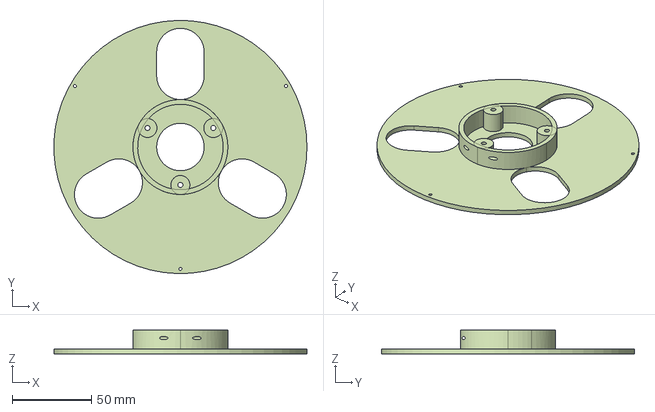
[picture p82: CAD file, 2018-10-31]
MiniSpool/MiniSpoolHalf2_15MM.fcstd
159.9 x 159.9 x 15.0 mm
