DarkCaster/3DPrintingStuff/Other/SensorsClip.FCStd

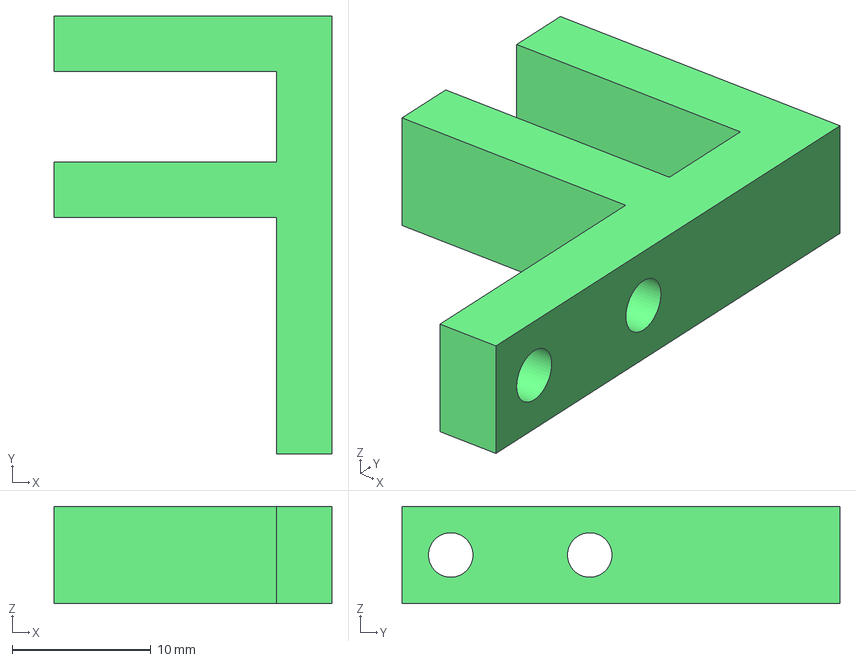
[picture p83: CAD file, 2018-09-25]
Other/SensorsClip.FCStd
20.0 x 31.5 x 7.00 mm
