DarkCaster/3DPrintingStuff/RepRap_Huxley_CustomParts/BedClamping2_Alt1.FCStd

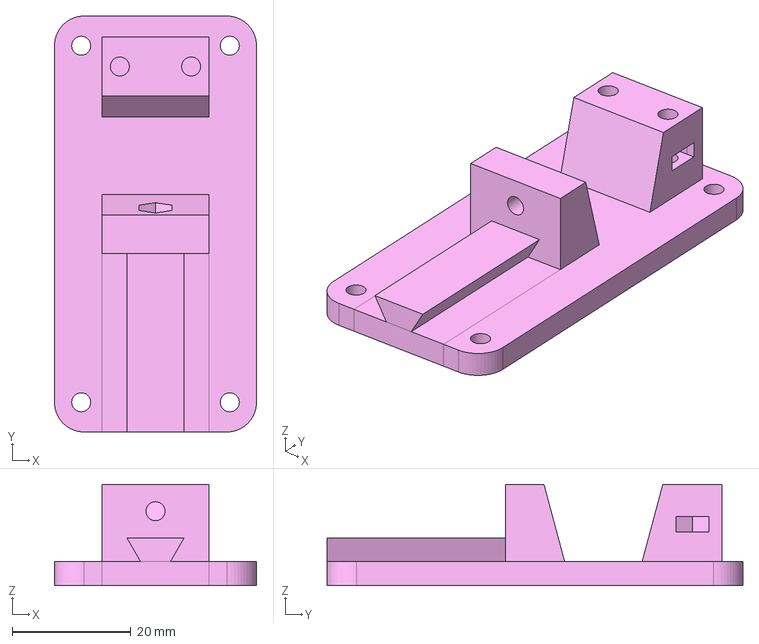
[picture p84: CAD file, 2018-10-01]
RepRap_Huxley_CustomParts/BedClamping2_Alt1.FCStd
34.0 x 70.0 x 17.0 mm
