DarkCaster/3DPrintingStuff/RepRap_Huxley_CustomParts/ExtruderDriveHolder/ExtruderDriveHolder2_Alt.FCStd

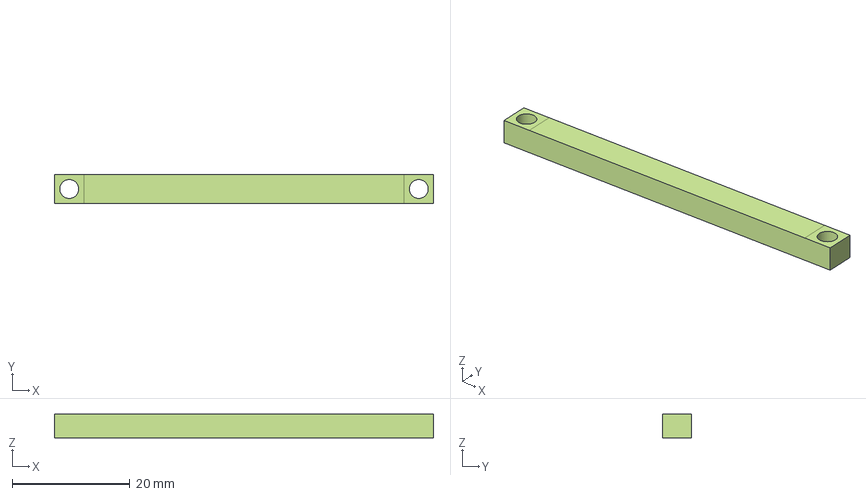
[picture p85: CAD file, 2018-10-09]
RepRap_Huxley_CustomParts/ExtruderDriveHolder/ExtruderDriveHolder2_Alt.FCStd
64.3 x 5.00 x 4.00 mm
