DarkCaster/3DPrintingStuff/RepRap_Huxley_CustomParts/XAxis_Left/XEndstopClip2.FCStd

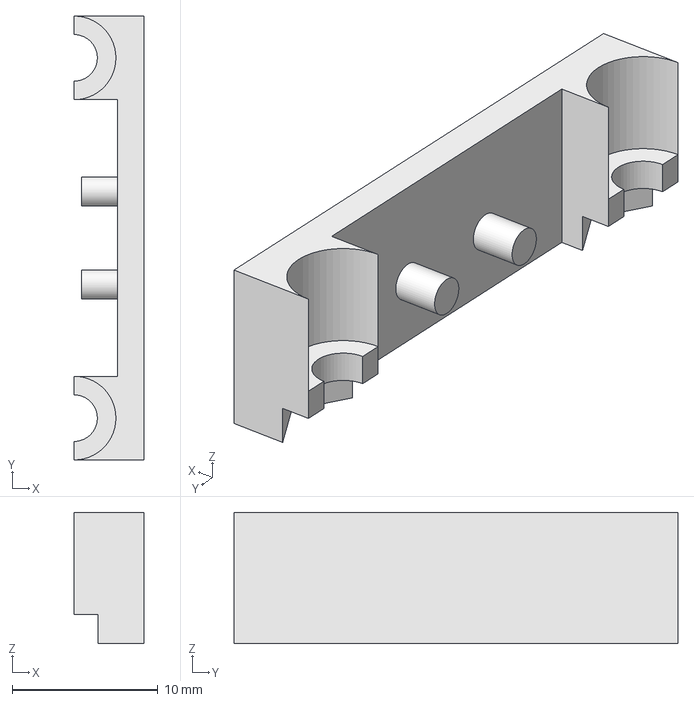
[picture p86: CAD file, 2019-01-17]
RepRap_Huxley_CustomParts/XAxis_Left/XEndstopClip2.FCStd
4.80 x 30.5 x 9.00 mm
