DarkCaster/3DPrintingStuff/RepRap_Huxley_CustomParts/XAxis_Right/RightXEnd_TensionerIdler.FCStd

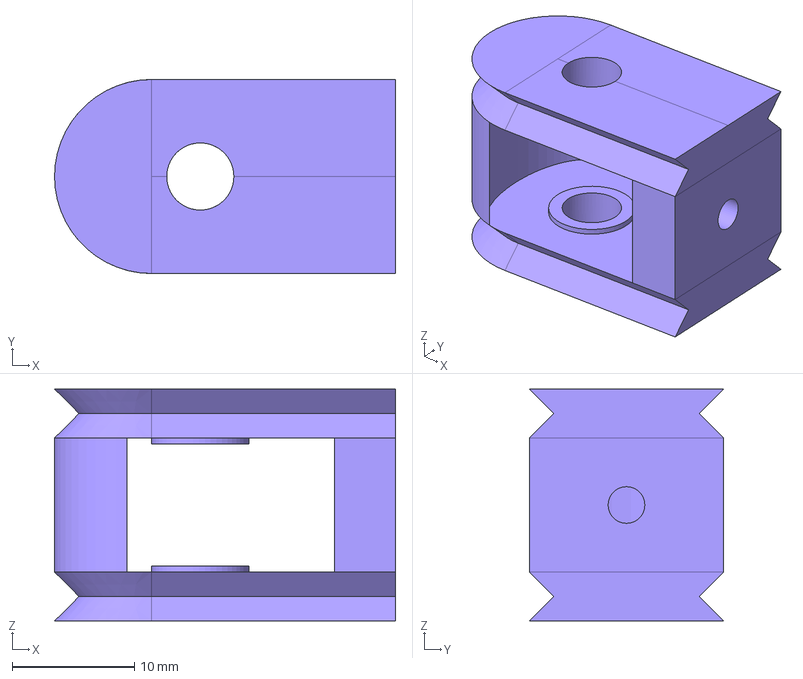
[picture p87: CAD file, 2018-12-28]
RepRap_Huxley_CustomParts/XAxis_Right/RightXEnd_TensionerIdler.FCStd
28.0 x 15.9 x 19.0 mm
