DarkCaster/3DPrintingStuff/RepRap_Huxley_CustomParts/XCarriage/BackClip.FCStd

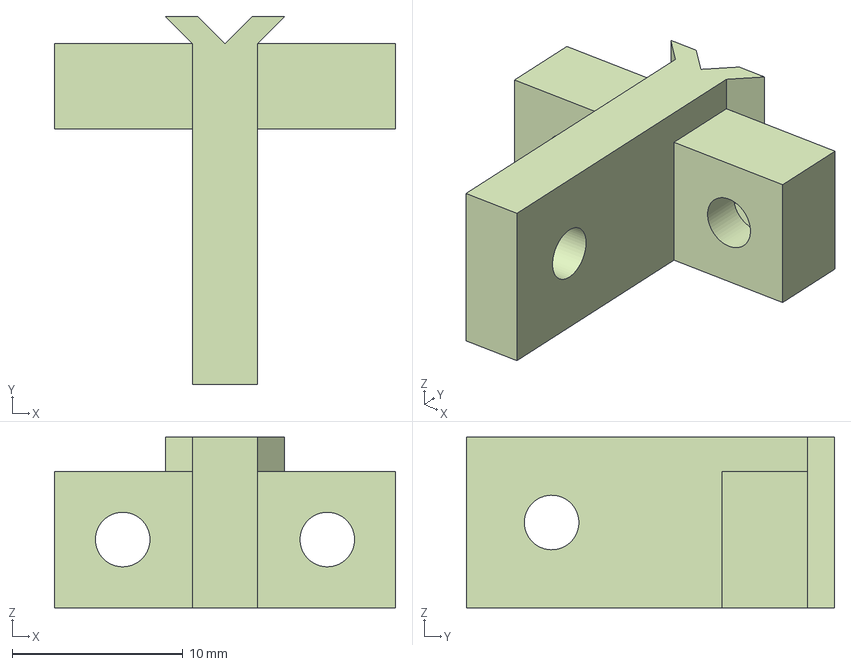
[picture p88: CAD file, 2019-01-11]
RepRap_Huxley_CustomParts/XCarriage/BackClip.FCStd
20.0 x 21.6 x 10.0 mm
