DarkCaster/3DPrintingStuff/MiniSpool/MiniSpoolHalf2.fcstd

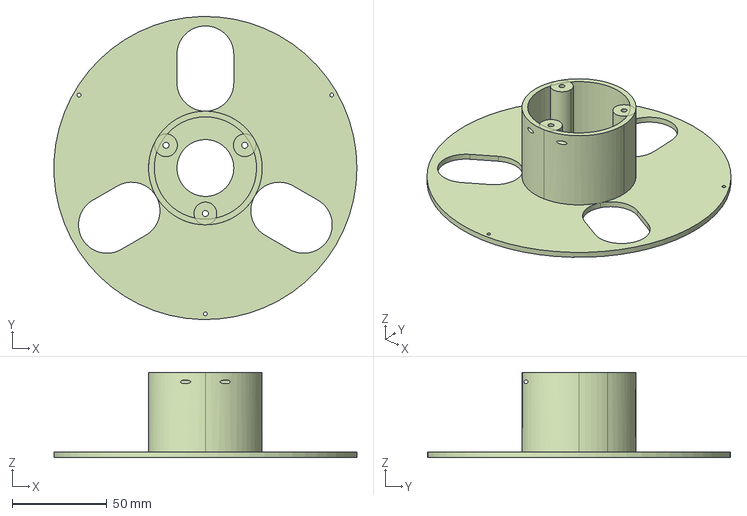
[picture p91: CAD file, 2018-10-30]
MiniSpool/MiniSpoolHalf2.fcstd
159.9 x 159.9 x 45.0 mm
