DarkCaster/3DPrintingStuff/Other/CaseStand_M6.FCStd

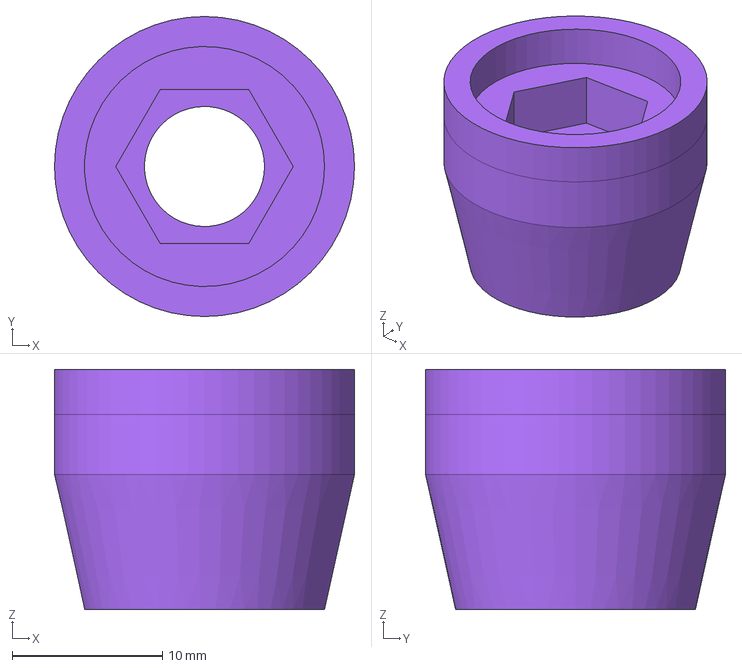
[picture p92: CAD file, 2018-09-25]
Other/CaseStand_M6.FCStd
20.0 x 20.0 x 16.0 mm
