DarkCaster/3DPrintingStuff/RepRap_Huxley_CustomParts/BedClamping1_Alt1.FCStd

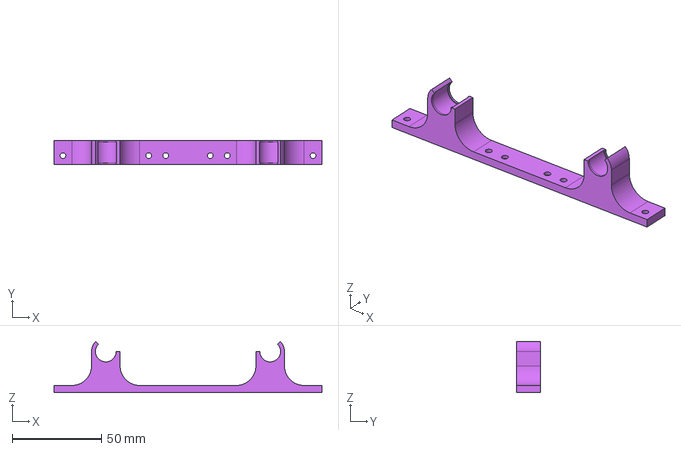
[picture p93: CAD file, 2018-10-01]
RepRap_Huxley_CustomParts/BedClamping1_Alt1.FCStd
150.0 x 13.5 x 28.7 mm
