DarkCaster/3DPrintingStuff/RepRap_Huxley_CustomParts/Helpers/Rod_M8x80mm.FCStd

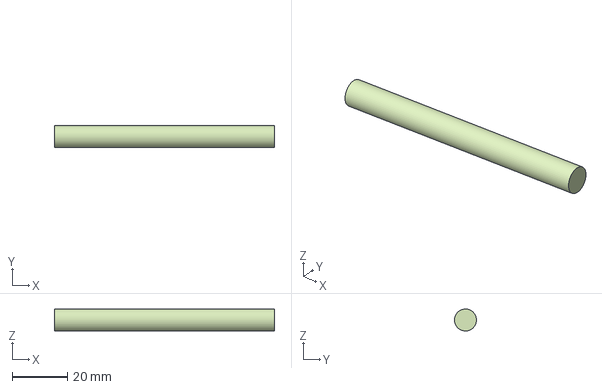
[picture p94: CAD file, 2019-01-15]
RepRap_Huxley_CustomParts/Helpers/Rod_M8x80mm.FCStd
80.0 x 7.99 x 8.00 mm
