DarkCaster/3DPrintingStuff/RepRap_Huxley_CustomParts/Other/XZAlignmentTool.fcstd

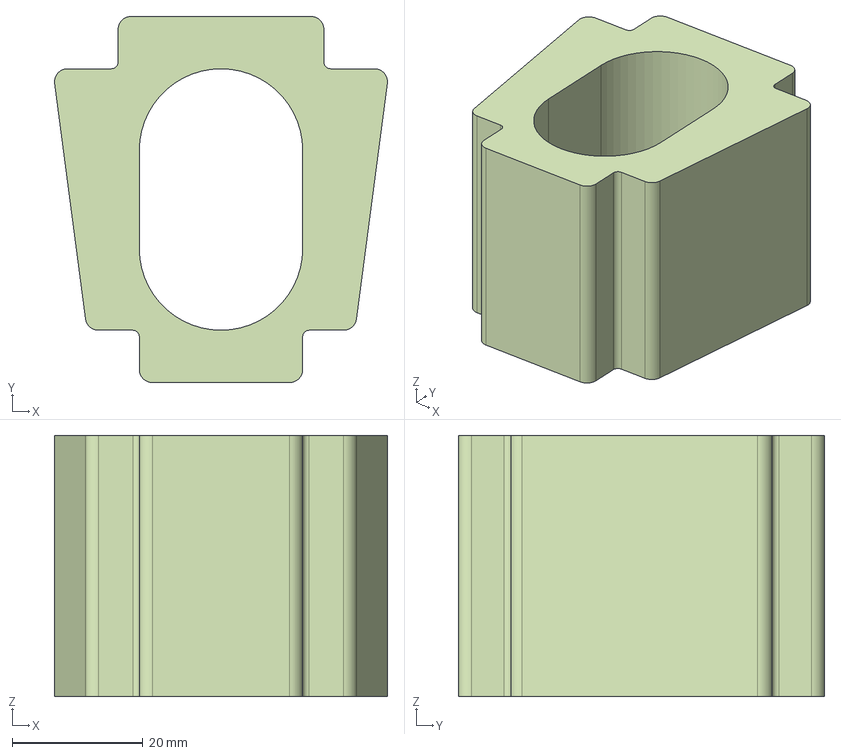
[picture p95: CAD file, 2018-11-06]
RepRap_Huxley_CustomParts/Other/XZAlignmentTool.fcstd
50.9 x 56.0 x 40.0 mm
