DarkCaster/3DPrintingStuff/RepRap_Huxley_CustomParts/XAxis_Left/ZThreaderRodClip_THSL-200-8D.FCStd

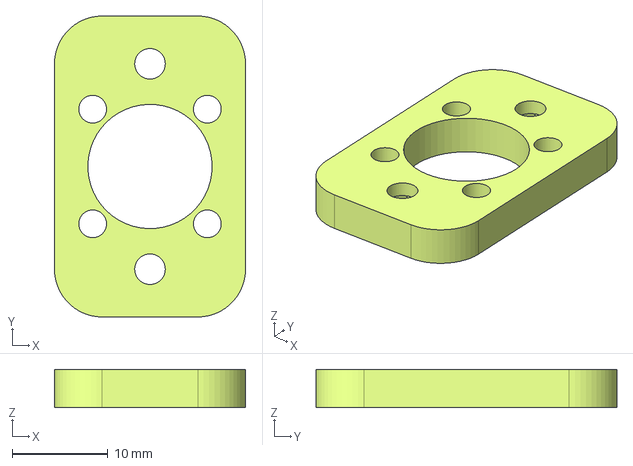
[picture p96: CAD file, 2019-01-15]
RepRap_Huxley_CustomParts/XAxis_Left/ZThreaderRodClip_THSL-200-8D.FCStd
20.0 x 31.5 x 4.00 mm
