DarkCaster/3DPrintingStuff/RepRap_Huxley_CustomParts/XAxis_Right/RightXEnd_TensionerStand.FCStd

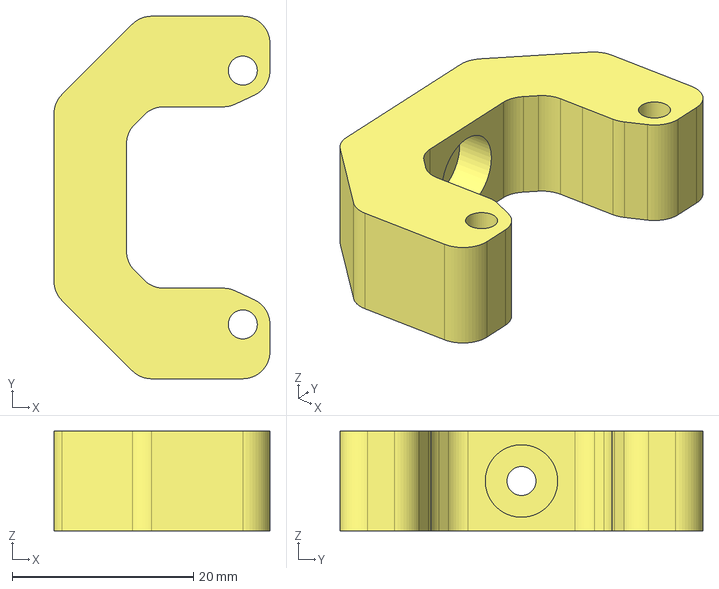
[picture p97: CAD file, 2018-12-28]
RepRap_Huxley_CustomParts/XAxis_Right/RightXEnd_TensionerStand.FCStd
23.8 x 40.0 x 11.0 mm
