DarkCaster/3DPrintingStuff/RepRap_Huxley_CustomParts/XCarriage/FrontFanCaseClip_40x40.FCStd

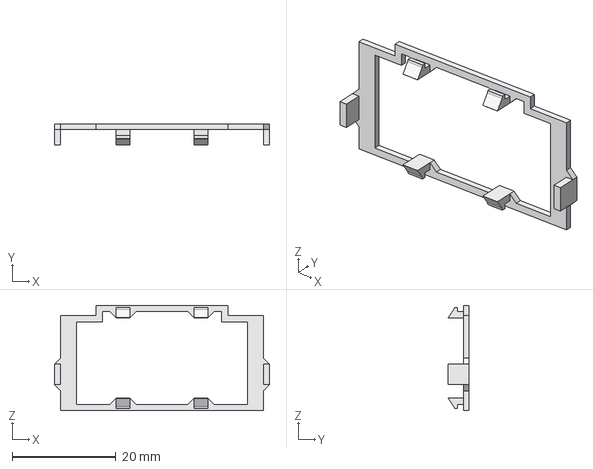
[picture p98: CAD file, 2019-01-11]
RepRap_Huxley_CustomParts/XCarriage/FrontFanCaseClip_40x40.FCStd
41.4 x 4.00 x 20.3 mm
