DarkCaster/3DPrintingStuff/RepRap_Huxley_CustomParts/YAxis/BedBeltClamp2_Alt2.FCStd

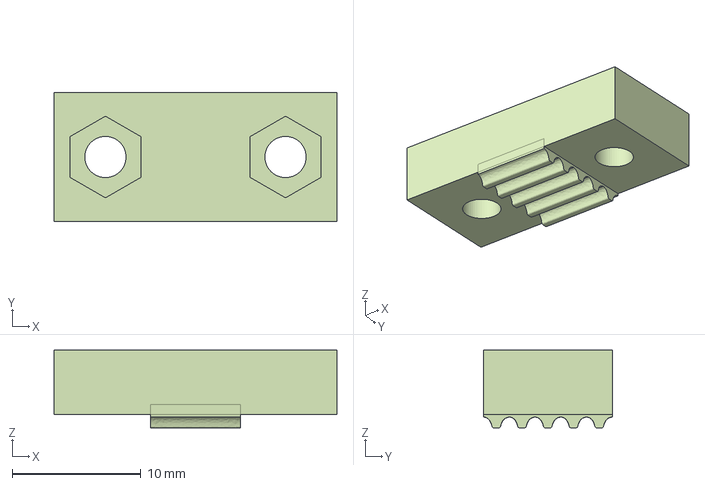
[picture p99: CAD file, 2018-10-04]
RepRap_Huxley_CustomParts/YAxis/BedBeltClamp2_Alt2.FCStd
22.0 x 10.0 x 6.05 mm
