DarkCaster/3DPrintingStuff/GearedExtruderDrive_V1_NEMA17/Base_623zz+M3.FCStd

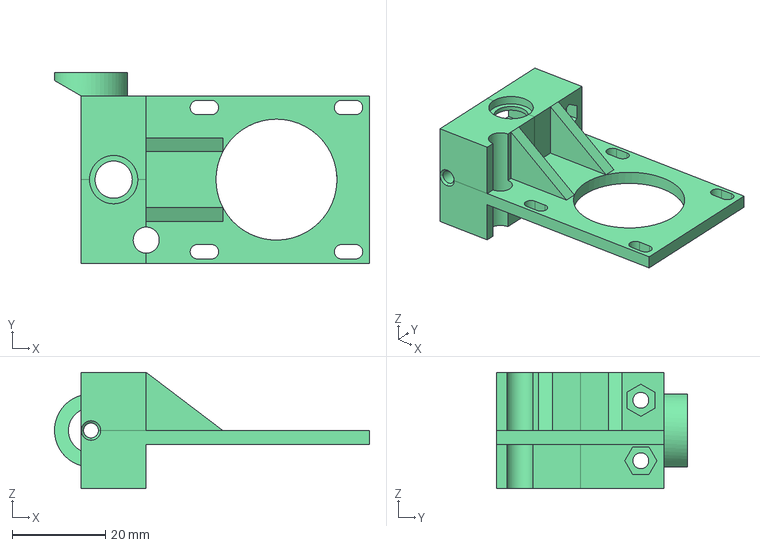
[picture p100: CAD file, 2018-05-31]
GearedExtruderDrive_V1_NEMA17/Base_623zz+M3.FCStd
67.7 x 41.0 x 25.0 mm
