DarkCaster/3DPrintingStuff/RepRap_Huxley_CustomParts/BedBeltClamp2_Alt.FCStd

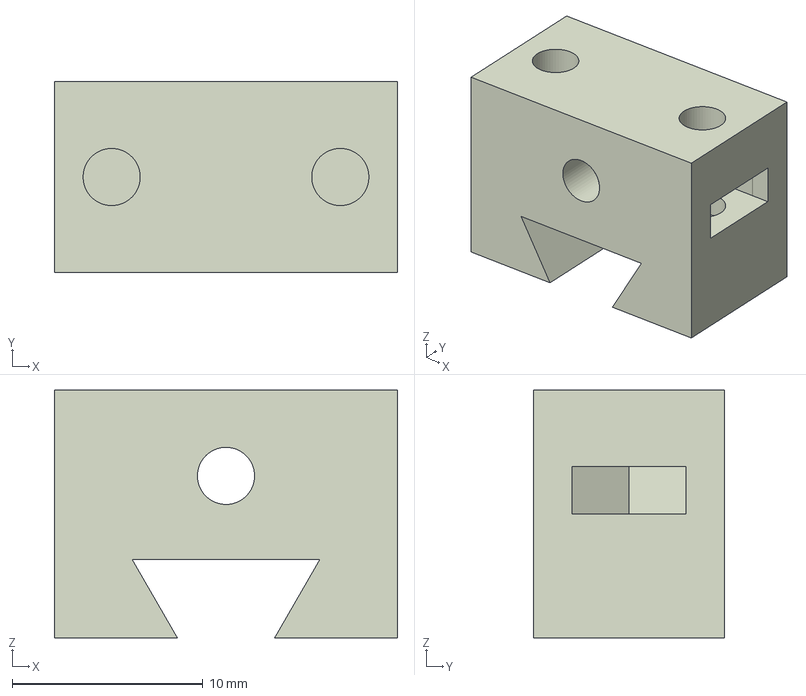
[picture p101: CAD file, 2018-10-01]
RepRap_Huxley_CustomParts/BedBeltClamp2_Alt.FCStd
18.0 x 10.0 x 13.0 mm
