DarkCaster/3DPrintingStuff/RepRap_Huxley_CustomParts/Helpers/Huxley_Z_Motor_Bracket.FCStd

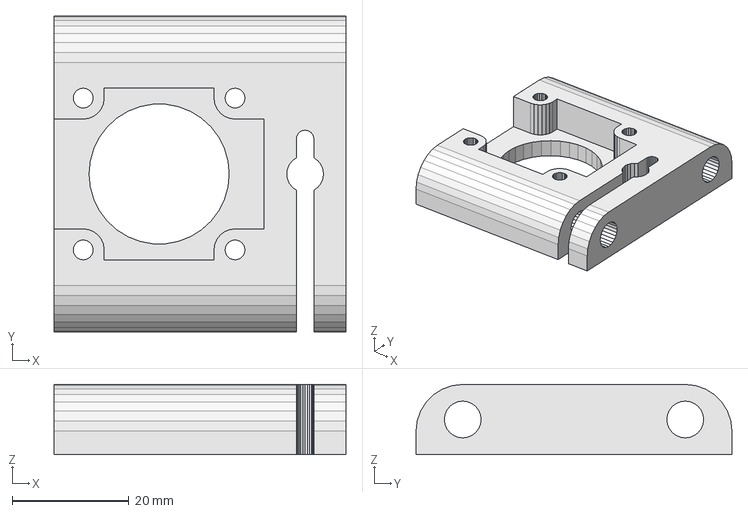
[picture p102: CAD file, 2019-01-15]
RepRap_Huxley_CustomParts/Helpers/Huxley_Z_Motor_Bracket.FCStd
50.0 x 54.1 x 12.0 mm
