DarkCaster/3DPrintingStuff/RepRap_Huxley_CustomParts/Other/FrameTensionerClip_M5.FCStd

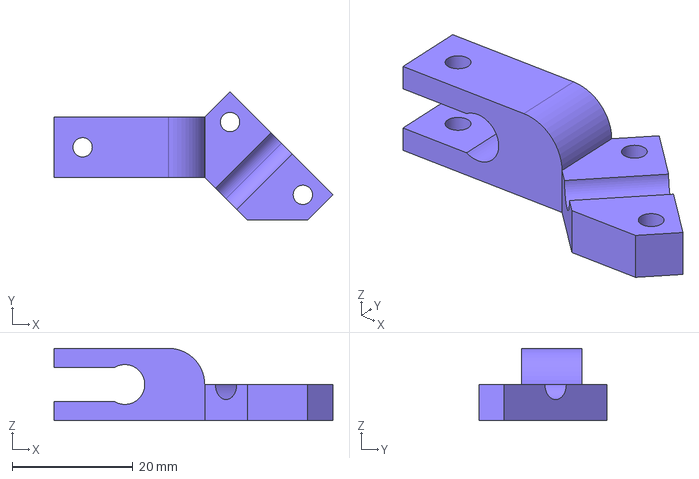
[picture p103: CAD file, 2018-10-05]
RepRap_Huxley_CustomParts/Other/FrameTensionerClip_M5.FCStd
46.3 x 21.3 x 12.0 mm
