DarkCaster/3DPrintingStuff/RepRap_Huxley_CustomParts/XAxis_Right/BeltPulley_2x623zz_FCGearAddon.FCStd

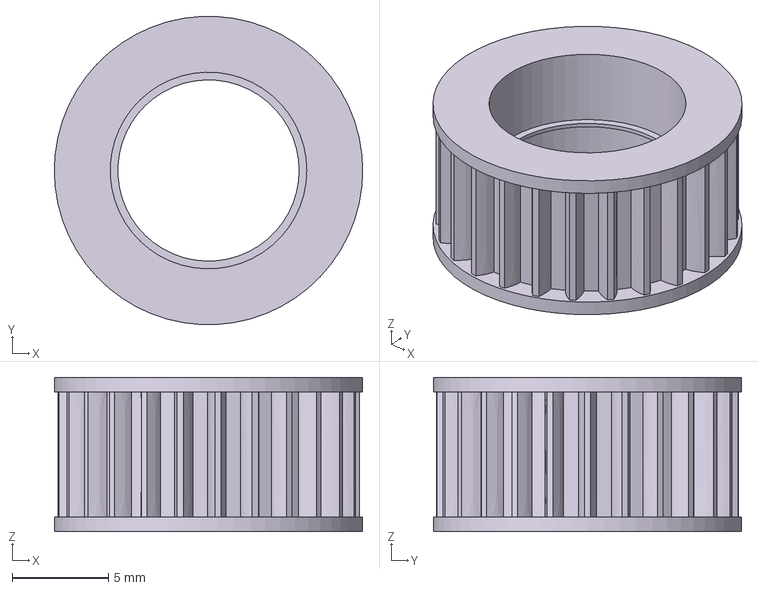
[picture p104: CAD file, 2018-07-22]
RepRap_Huxley_CustomParts/XAxis_Right/BeltPulley_2x623zz_FCGearAddon.FCStd
16.0 x 16.0 x 8.00 mm
