DarkCaster/3DPrintingStuff/RepRap_Huxley_CustomParts/XCarriage/HotendFrontFanCase_40x40.FCStd

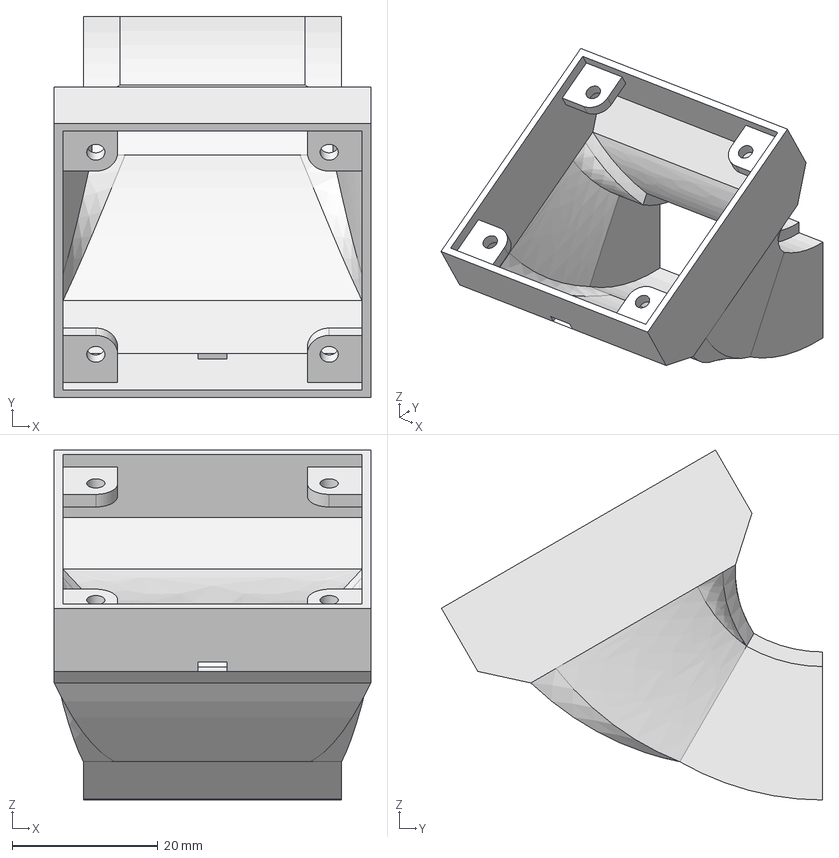
[picture p105: CAD file, 2019-01-11]
RepRap_Huxley_CustomParts/XCarriage/HotendFrontFanCase_40x40.FCStd
43.4 x 52.3 x 48.0 mm
