DarkCaster/3DPrintingStuff/RepRap_Huxley_CustomParts/YAxis/YEndStopClip.FCStd

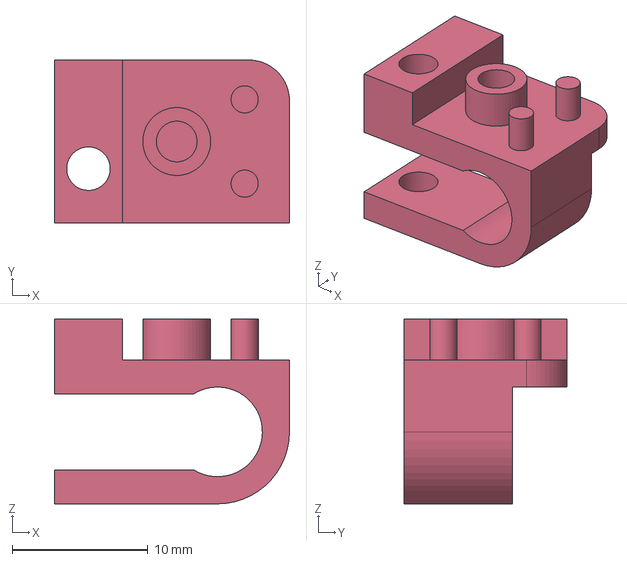
[picture p106: CAD file, 2018-09-01]
RepRap_Huxley_CustomParts/YAxis/YEndStopClip.FCStd
17.3 x 12.0 x 13.6 mm
