DarkCaster/3DPrintingStuff/GearedExtruderDrive_V1_NEMA17/LargeGear_V1_M3.FCStd

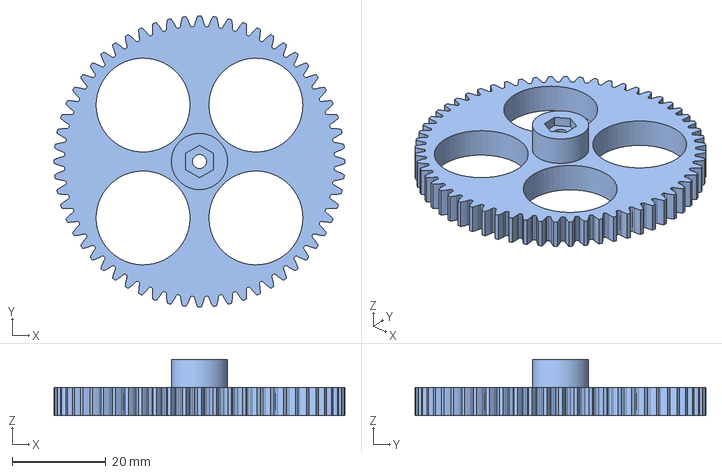
[picture p107: CAD file, 2018-05-31]
GearedExtruderDrive_V1_NEMA17/LargeGear_V1_M3.FCStd
62.0 x 62.0 x 12.0 mm
