DarkCaster/3DPrintingStuff/RepRap_Huxley_CustomParts/Helpers/Hotend_E3D_Dummy_Outer.FCStd

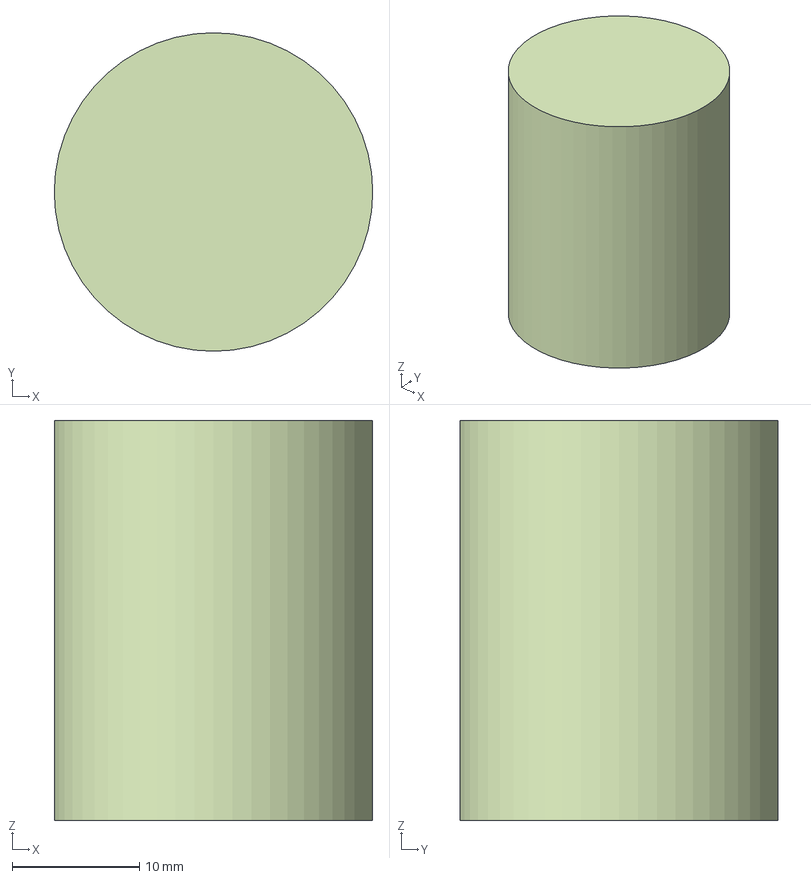
[picture p108: CAD file, 2019-01-04]
RepRap_Huxley_CustomParts/Helpers/Hotend_E3D_Dummy_Outer.FCStd
25.0 x 25.0 x 31.4 mm
