DarkCaster/3DPrintingStuff/RepRap_Huxley_CustomParts/XAxis_Right/RightXEnd_TensionerKnob.FCStd

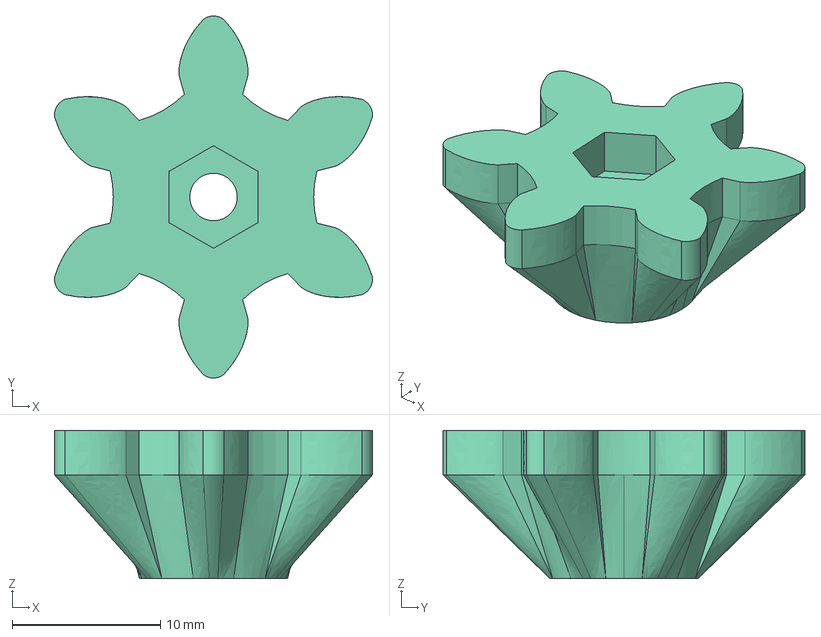
[picture p110: CAD file, 2018-07-19]
RepRap_Huxley_CustomParts/XAxis_Right/RightXEnd_TensionerKnob.FCStd
21.5 x 24.4 x 10.0 mm
