DarkCaster/3DPrintingStuff/RepRap_Huxley_CustomParts/XCarriage/HotendClippingRightHalf_E3DV6_Bowden.FCStd

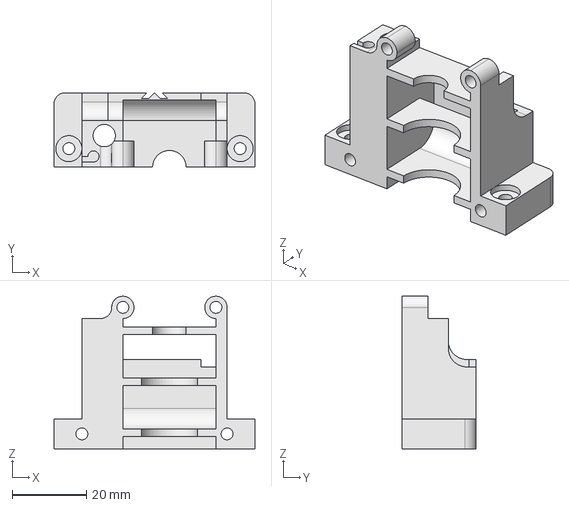
[picture p111: CAD file, 2019-01-06]
RepRap_Huxley_CustomParts/XCarriage/HotendClippingRightHalf_E3DV6_Bowden.FCStd
54.0 x 20.0 x 41.0 mm
