DarkCaster/3DPrintingStuff/RepRap_Huxley_CustomParts/YAxis/YEndStopClip2.FCStd

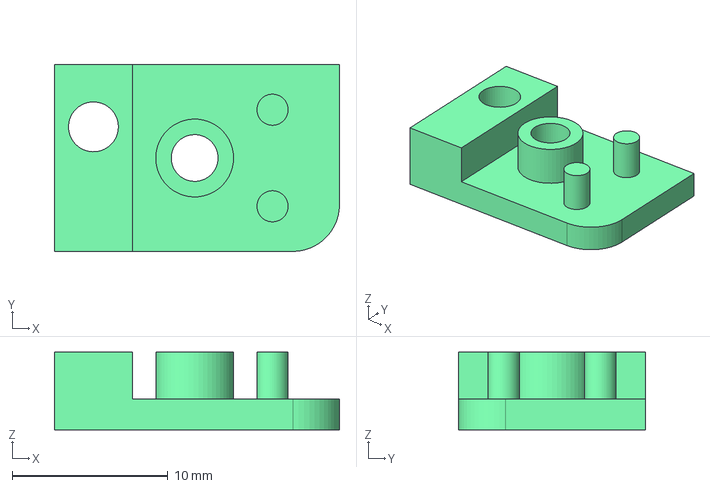
[picture p112: CAD file, 2018-08-31]
RepRap_Huxley_CustomParts/YAxis/YEndStopClip2.FCStd
18.3 x 12.0 x 5.00 mm
