DarkCaster/3DPrintingStuff/RepRap_Huxley_CustomParts/ZEndStopClip4.FCStd

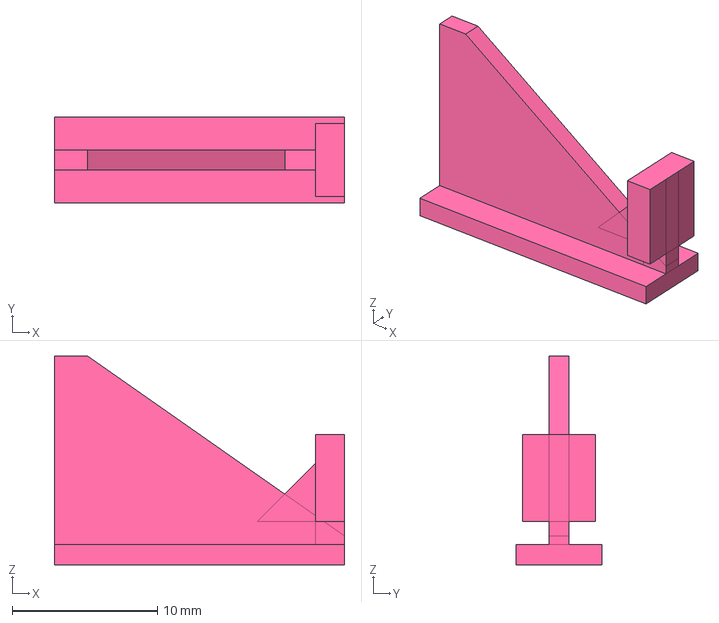
[picture p113: CAD file, 2018-09-20]
RepRap_Huxley_CustomParts/ZEndStopClip4.FCStd
20.0 x 5.90 x 14.4 mm
