DarkCaster/3DPrintingStuff/GearedExtruderDrive_V1_NEMA17/IdlerClip_B.FCStd

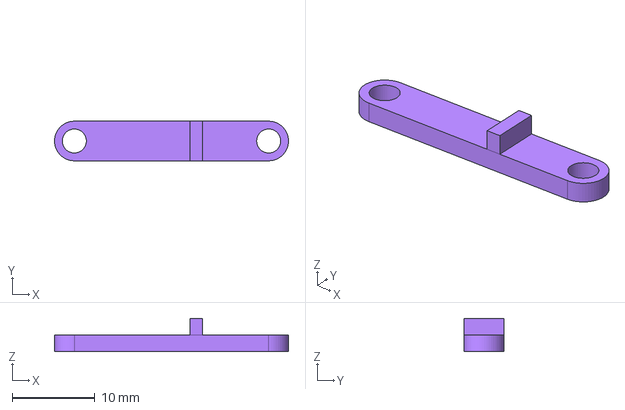
[picture p114: CAD file, 2018-05-21]
GearedExtruderDrive_V1_NEMA17/IdlerClip_B.FCStd
28.3 x 4.80 x 4.00 mm
