DarkCaster/3DPrintingStuff/RepRap_Huxley_CustomParts/Helpers/Hotend_E3D_Dummy.FCStd

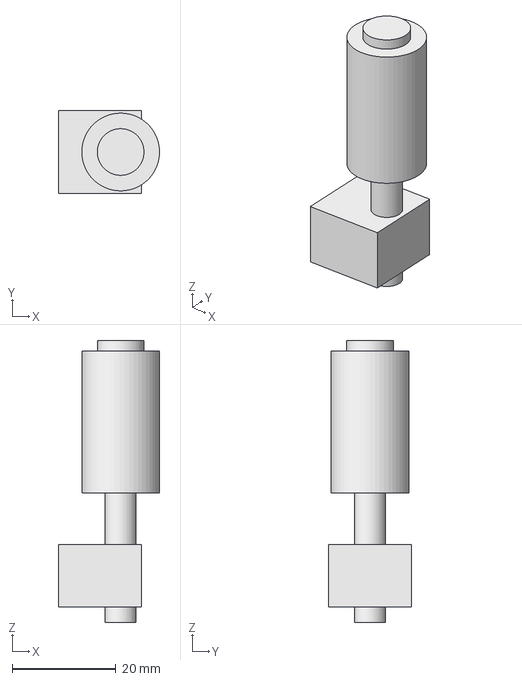
[picture p115: CAD file, 2019-01-02]
RepRap_Huxley_CustomParts/Helpers/Hotend_E3D_Dummy.FCStd
19.5 x 16.0 x 54.4 mm
