DarkCaster/3DPrintingStuff/RepRap_Huxley_CustomParts/XAxis_Right/BeltPulley_2x685zz_FCGearAddon.FCStd

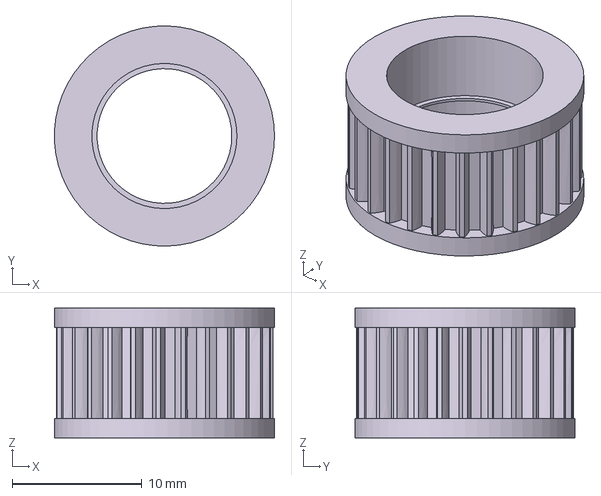
[picture p116: CAD file, 2018-07-19]
RepRap_Huxley_CustomParts/XAxis_Right/BeltPulley_2x685zz_FCGearAddon.FCStd
17.0 x 17.0 x 10.0 mm
