DarkCaster/3DPrintingStuff/RepRap_Huxley_CustomParts/XCarriage/HotendClippingLeftHalf_E3DV6_Bowden.FCStd

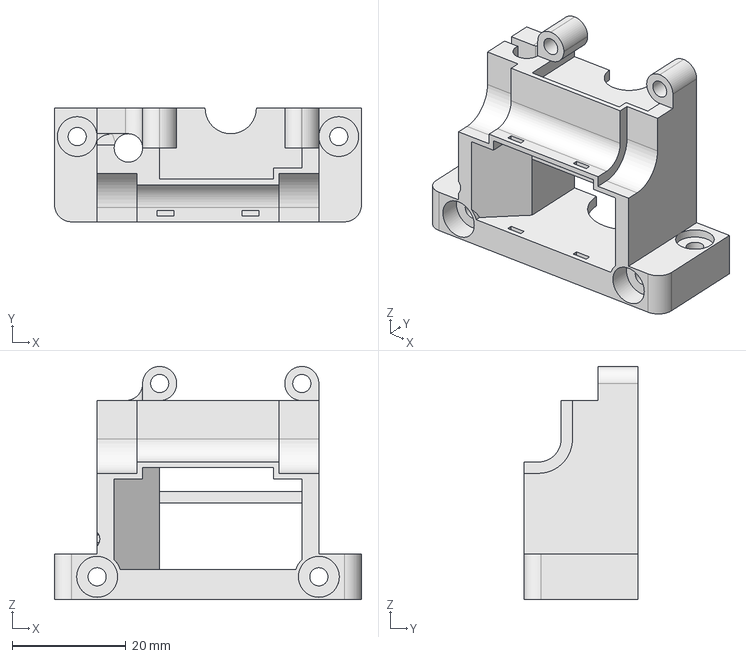
[picture p117: CAD file, 2019-01-05]
RepRap_Huxley_CustomParts/XCarriage/HotendClippingLeftHalf_E3DV6_Bowden.FCStd
54.0 x 20.0 x 41.0 mm
