DarkCaster/3DPrintingStuff/RepRap_Huxley_CustomParts/ZEndStopClip3.FCStd

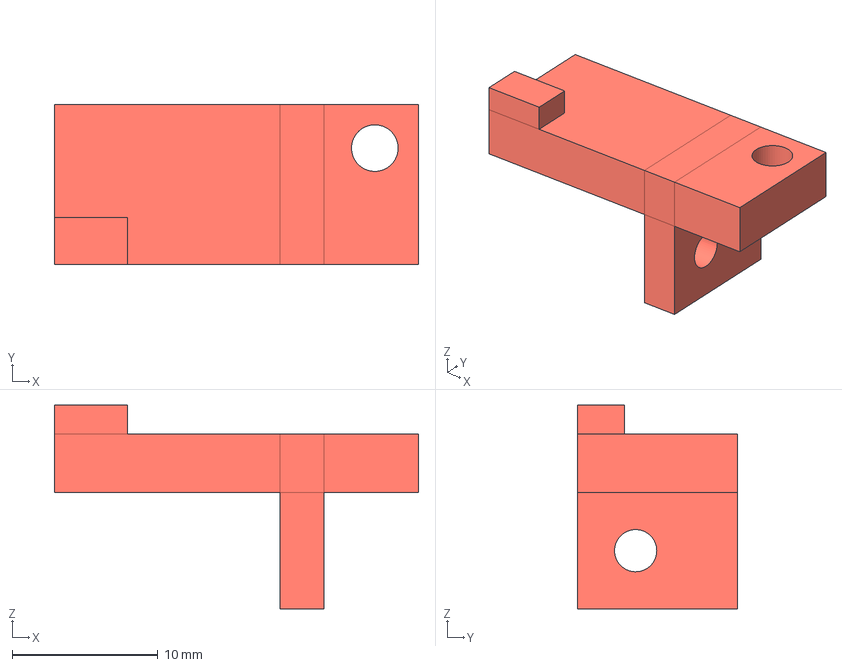
[picture p118: CAD file, 2018-09-18]
RepRap_Huxley_CustomParts/ZEndStopClip3.FCStd
25.0 x 11.0 x 14.0 mm
