DarkCaster/3DPrintingStuff/GearedExtruderDrive_V1_NEMA17/IdlerClip_A.FCStd

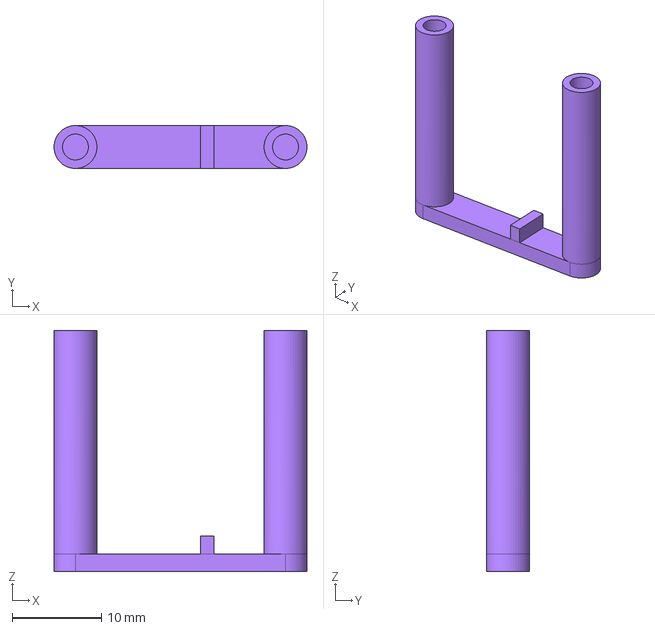
[picture p119: CAD file, 2018-05-21]
GearedExtruderDrive_V1_NEMA17/IdlerClip_A.FCStd
28.3 x 4.80 x 27.0 mm
