DarkCaster/3DPrintingStuff/RepRap_Huxley_CustomParts/Helpers/Rod_M6x320mm.FCStd

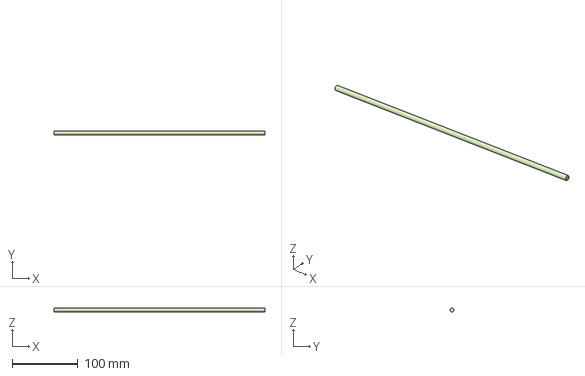
[picture p120: CAD file, 2018-12-29]
RepRap_Huxley_CustomParts/Helpers/Rod_M6x320mm.FCStd
320.0 x 5.99 x 6.00 mm
