DarkCaster/3DPrintingStuff/RepRap_Huxley_CustomParts/XCarriage/CarriageHalf_Bottom.FCStd

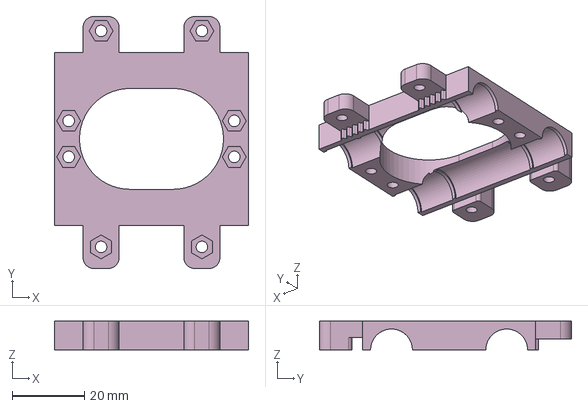
[picture p121: CAD file, 2018-12-20]
RepRap_Huxley_CustomParts/XCarriage/CarriageHalf_Bottom.FCStd
54.0 x 70.0 x 8.00 mm
