DarkCaster/3DPrintingStuff/GearedExtruderDrive_V1_NEMA17/M3_to_M5_Adapter.FCStd

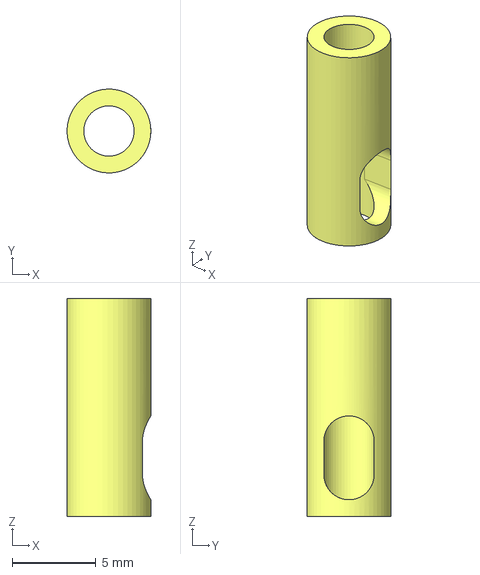
[picture p122: CAD file, 2018-05-21]
GearedExtruderDrive_V1_NEMA17/M3_to_M5_Adapter.FCStd
5.00 x 5.00 x 13.0 mm
