DarkCaster/3DPrintingStuff/RepRap_Huxley_CustomParts/Other/RRD_FGSC_Case2.FCStd

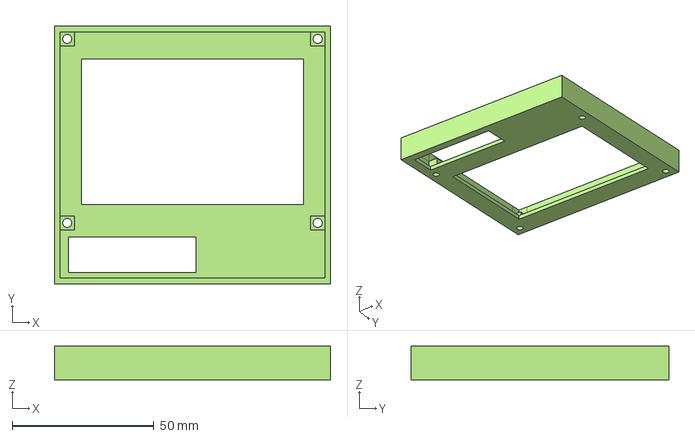
[picture p123: CAD file, 2018-09-28]
RepRap_Huxley_CustomParts/Other/RRD_FGSC_Case2.FCStd
97.5 x 91.0 x 12.0 mm
