DarkCaster/3DPrintingStuff/RepRap_Huxley_CustomParts/XEndStopClip2.FCStd

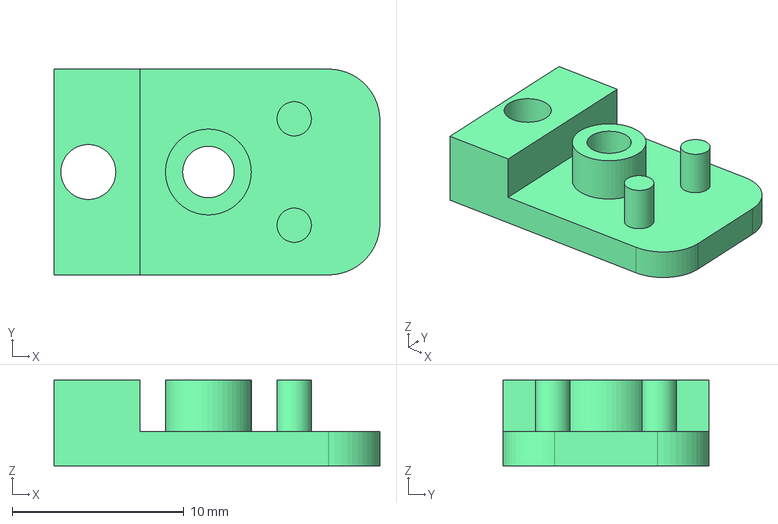
[picture p124: CAD file, 2018-08-30]
RepRap_Huxley_CustomParts/XEndStopClip2.FCStd
19.0 x 12.0 x 5.00 mm
