DarkCaster/3DPrintingStuff/GearedExtruderDrive_V1_NEMA17/Idler_623zz+M3.FCStd

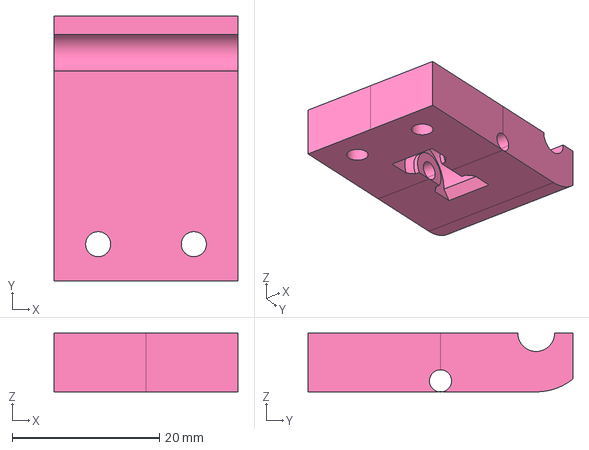
[picture p125: CAD file, 2018-05-21]
GearedExtruderDrive_V1_NEMA17/Idler_623zz+M3.FCStd
25.0 x 36.0 x 8.00 mm
