DarkCaster/3DPrintingStuff/RepRap_Huxley_CustomParts/Other/RRD_FGSC_Case1.FCStd

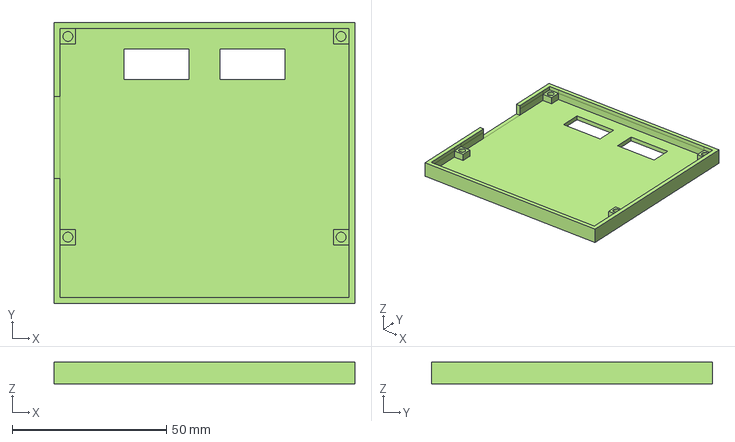
[picture p126: CAD file, 2018-09-28]
RepRap_Huxley_CustomParts/Other/RRD_FGSC_Case1.FCStd
97.5 x 91.0 x 7.00 mm
