DarkCaster/3DPrintingStuff/RepRap_Huxley_CustomParts/XCarriage/HotendExtraFanCasing.FCStd

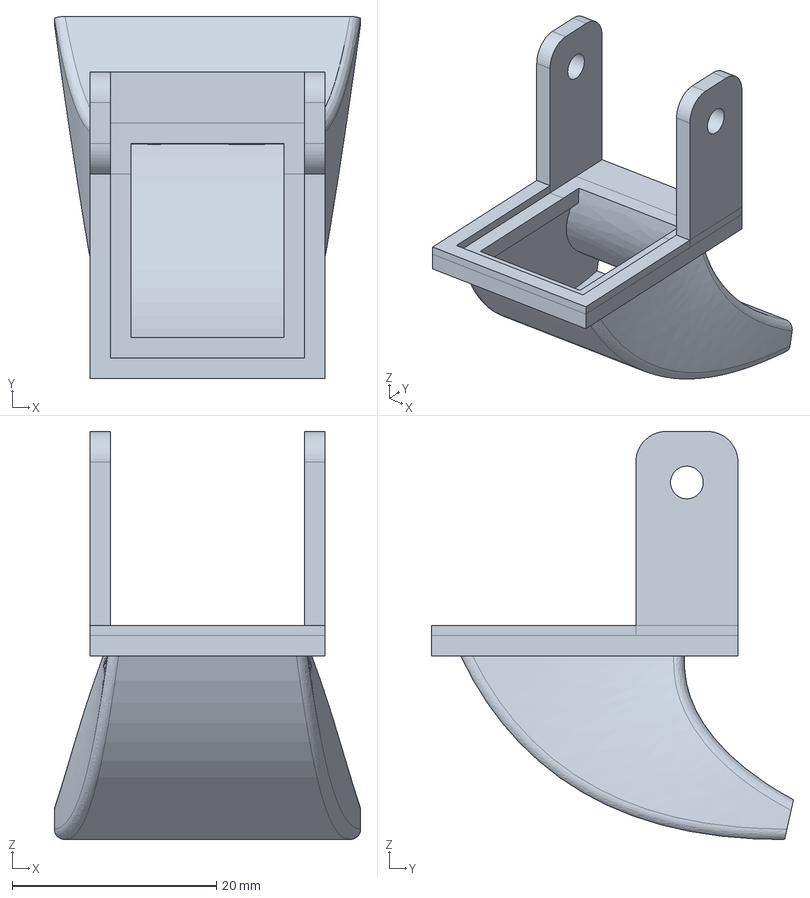
[picture p127: CAD file, 2018-09-11]
RepRap_Huxley_CustomParts/XCarriage/HotendExtraFanCasing.FCStd
30.0 x 35.4 x 40.0 mm
