DarkCaster/3DPrintingStuff/RepRap_Huxley_CustomParts/XEndStopClip.FCStd

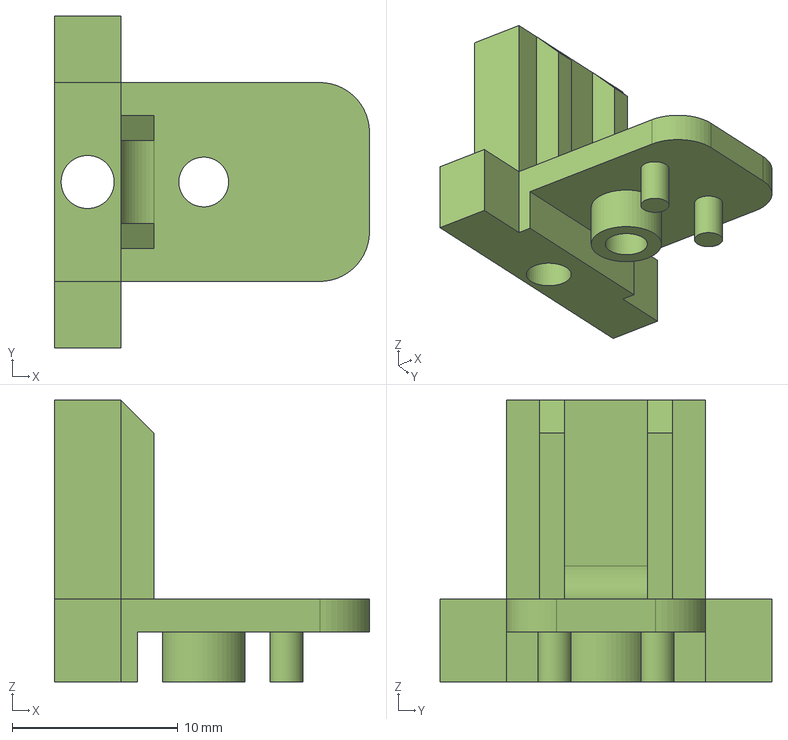
[picture p128: CAD file, 2018-08-30]
RepRap_Huxley_CustomParts/XEndStopClip.FCStd
19.0 x 20.0 x 17.0 mm
