DarkCaster/3DPrintingStuff/RepRap_Huxley_CustomParts/Other/Knob_M3.FCStd

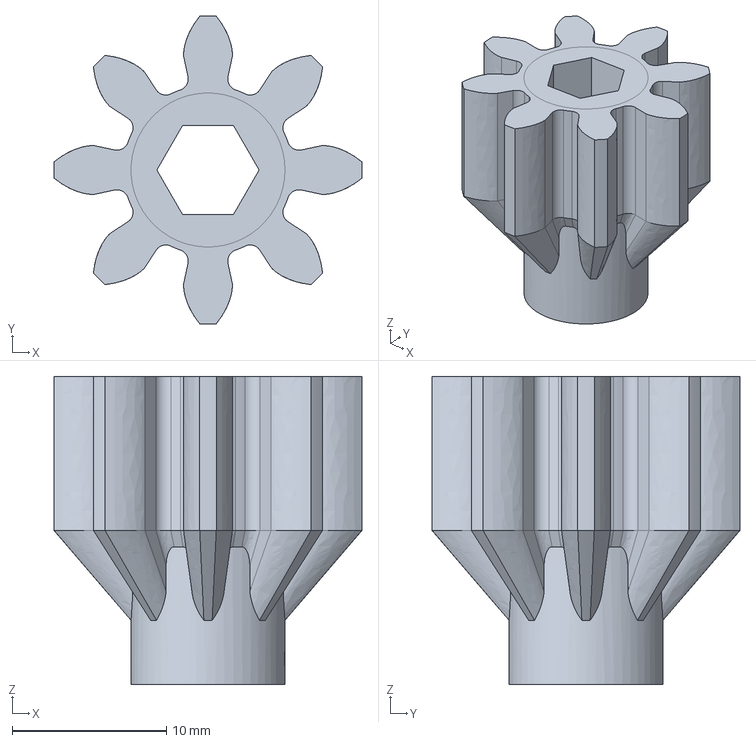
[picture p129: CAD file, 2018-09-18]
RepRap_Huxley_CustomParts/Other/Knob_M3.FCStd
20.0 x 20.0 x 20.0 mm
