DarkCaster/3DPrintingStuff/RepRap_Huxley_CustomParts/XCarriage/HotendClippingExtraFanTurbine.FCStd

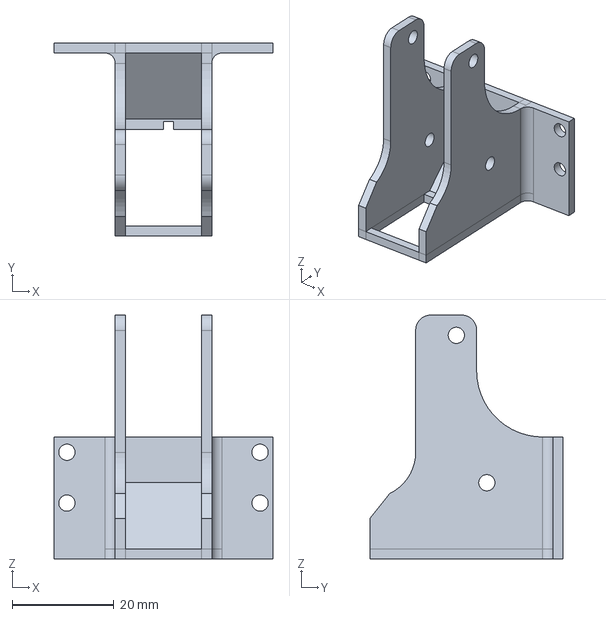
[picture p130: CAD file, 2018-09-10]
RepRap_Huxley_CustomParts/XCarriage/HotendClippingExtraFanTurbine.FCStd
43.0 x 38.0 x 48.0 mm
