DarkCaster/3DPrintingStuff/RepRap_Huxley_CustomParts/XEndStopClip3.FCStd

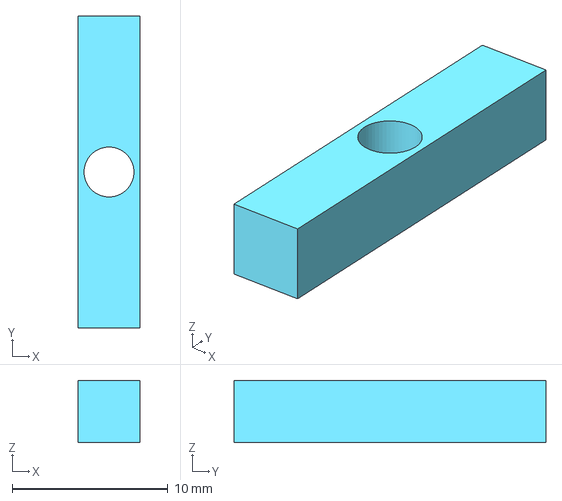
[picture p131: CAD file, 2018-08-30]
RepRap_Huxley_CustomParts/XEndStopClip3.FCStd
4.00 x 20.0 x 4.00 mm
