DarkCaster/3DPrintingStuff/RepRap_Huxley_CustomParts/ExtruderDriveHolder_NEMA17.FCStd

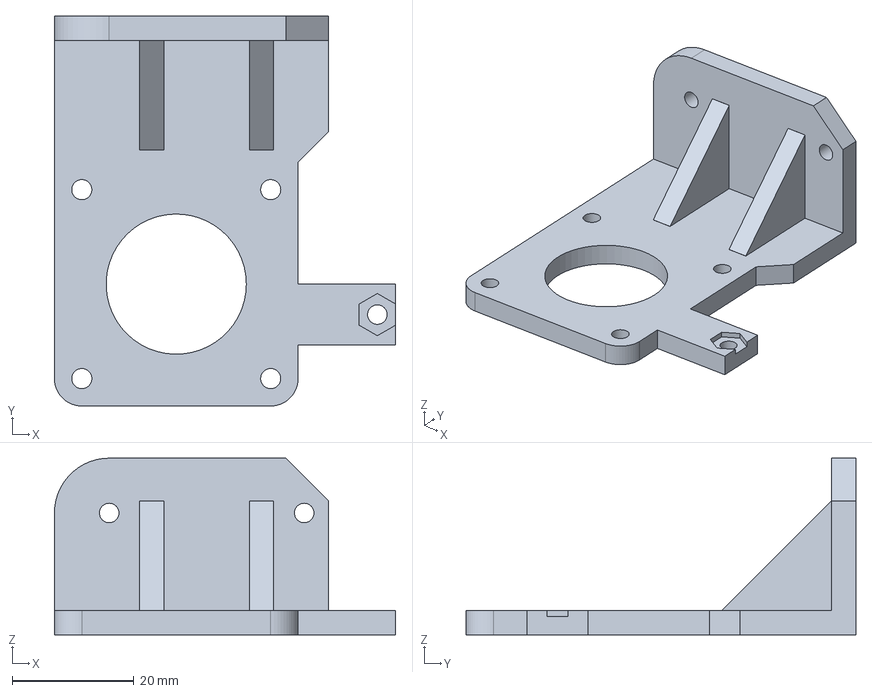
[picture p132: CAD file, 2018-08-20]
RepRap_Huxley_CustomParts/ExtruderDriveHolder_NEMA17.FCStd
56.0 x 64.0 x 29.0 mm
