DarkCaster/3DPrintingStuff/RepRap_Huxley_CustomParts/XCarriage/CarriageBeltClamp.FCStd

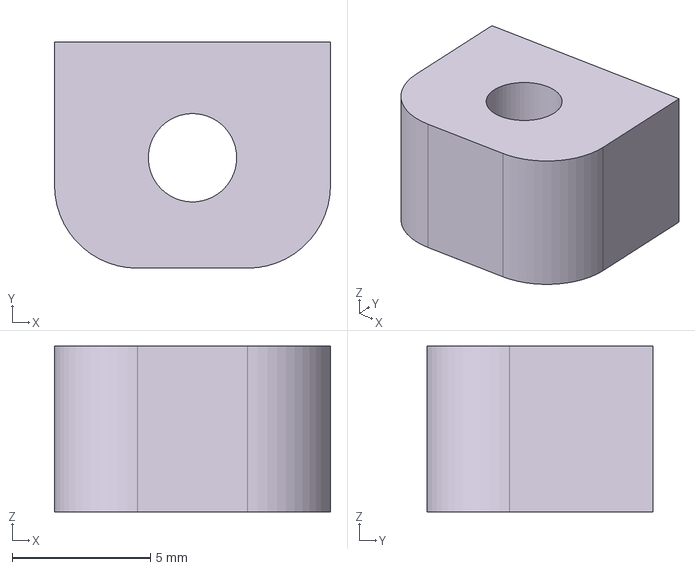
[picture p133: CAD file, 2018-07-24]
RepRap_Huxley_CustomParts/XCarriage/CarriageBeltClamp.FCStd
10.0 x 8.20 x 6.00 mm
