DarkCaster/3DPrintingStuff/RepRap_Huxley_CustomParts/ZThreadedRodClip2.FCStd

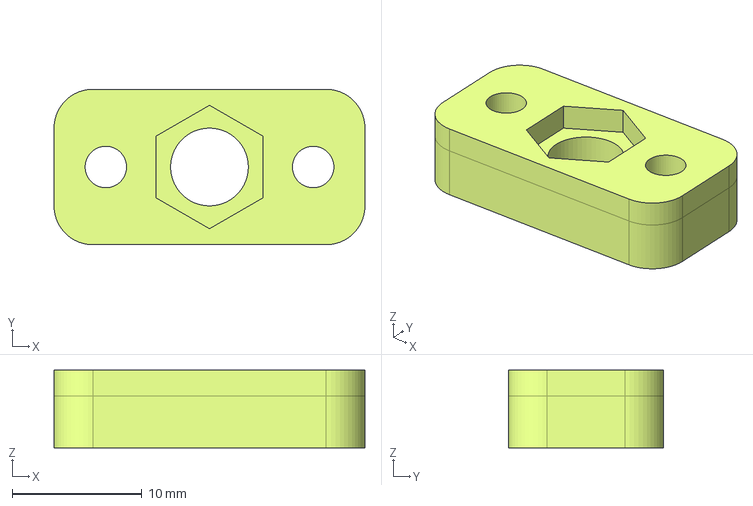
[picture p134: CAD file, 2018-07-31]
RepRap_Huxley_CustomParts/ZThreadedRodClip2.FCStd
24.0 x 12.0 x 6.00 mm
