DarkCaster/3DPrintingStuff/RepRap_Huxley_CustomParts/ZThreadedRodClip.FCStd

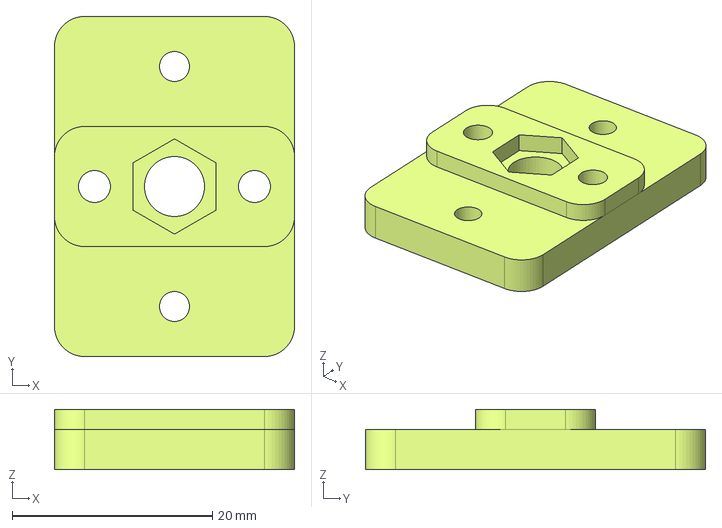
[picture p135: CAD file, 2018-07-31]
RepRap_Huxley_CustomParts/ZThreadedRodClip.FCStd
24.0 x 34.0 x 6.00 mm
