DarkCaster/3DPrintingStuff/RepRap_Huxley_CustomParts/CarriageHalf.FCStd

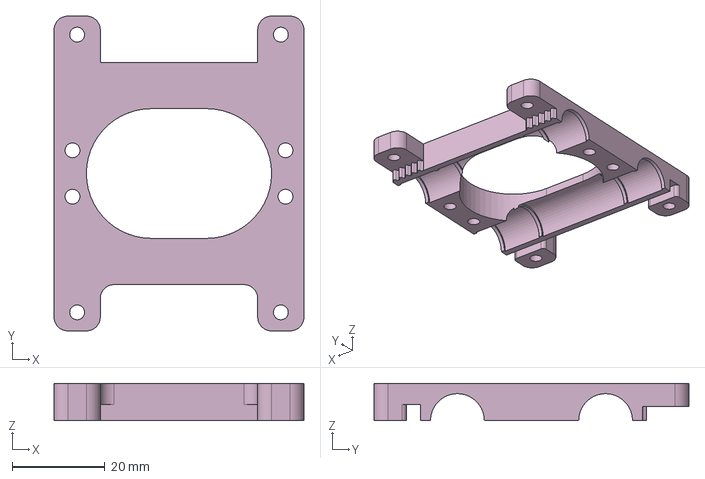
[picture p136: CAD file, 2018-07-24]
RepRap_Huxley_CustomParts/CarriageHalf.FCStd
54.0 x 68.0 x 8.00 mm
