DarkCaster/3DPrintingStuff/RepRap_Huxley_CustomParts/XBeltTensionerFrameStandNew.FCStd

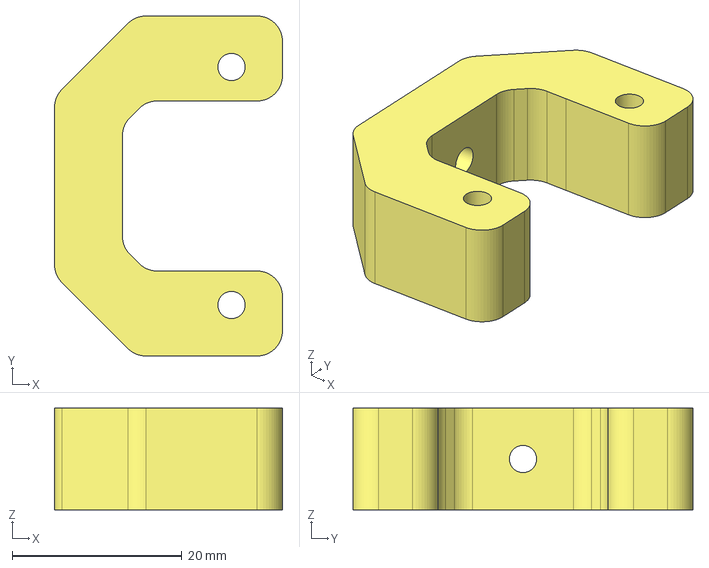
[picture p137: CAD file, 2018-07-24]
RepRap_Huxley_CustomParts/XBeltTensionerFrameStandNew.FCStd
26.8 x 40.0 x 12.0 mm
