DarkCaster/3DPrintingStuff/RepRap_Huxley_CustomParts/XBeltTensionerIdler.FCStd

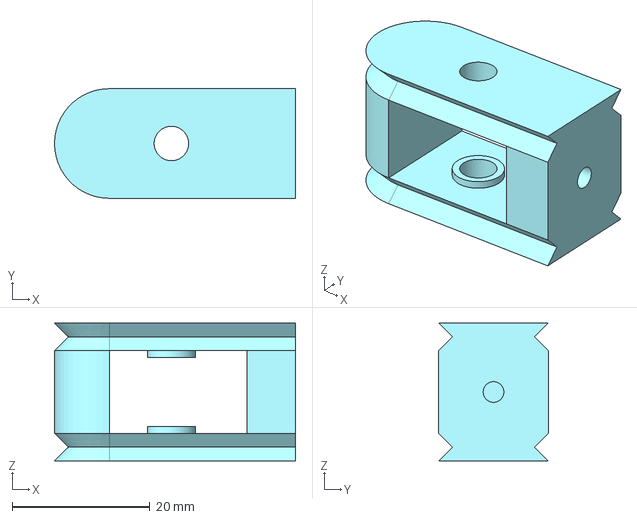
[picture p138: CAD file, 2018-07-24]
RepRap_Huxley_CustomParts/XBeltTensionerIdler.FCStd
35.0 x 15.9 x 20.0 mm
