DarkCaster/3DPrintingStuff/RepRap_Huxley_CustomParts/CarriageBeltClampNew.FCStd

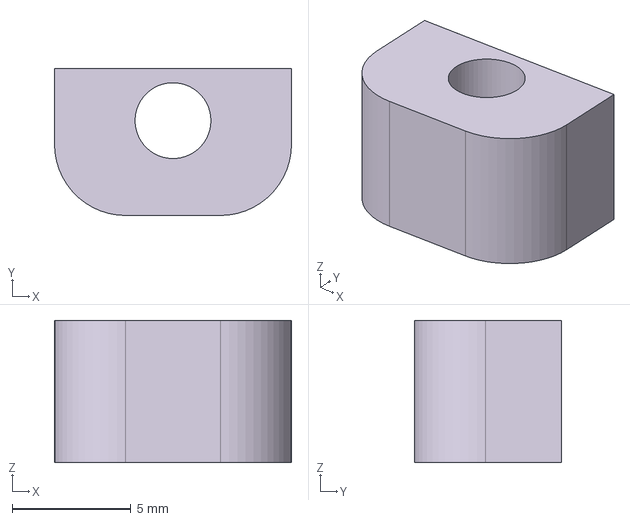
[picture p139: CAD file, 2018-07-21]
RepRap_Huxley_CustomParts/CarriageBeltClampNew.FCStd
10.0 x 6.20 x 6.00 mm
