DarkCaster/3DPrintingStuff/RepRap_Huxley_CustomParts/XBeltTensionerFrame.FCStd

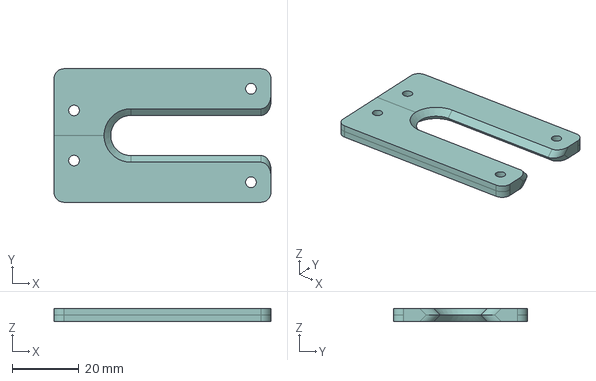
[picture p140: CAD file, 2018-07-19]
RepRap_Huxley_CustomParts/XBeltTensionerFrame.FCStd
65.0 x 40.0 x 4.00 mm
