DarkCaster/3DPrintingStuff/Kossel_Effector_Mount/HotendMount.scad

use <EffectorMount_Alt.scad>

module NutPocket
(
	nut_diam=6.65,
	pocket_len=100,
)
{
	m=(nut_diam/2)*sqrt(3)/2;
	cylinder(d=nut_diam,h=pocket_len,center=false,$fn=6);
}

module VNutPocket
(
	nut_diam=6.65,
	nut_height=2.8,
	pocket_len=10,
)
{
	m=(nut_diam/2)*sqrt(3)/2;
	rotate(a=90,v=[0,0,1])
		rotate(a=90,v=[0,-1,0])
			union()
			{
				cylinder(d=nut_diam,h=nut_height,center=true,$fn=6);
				translate([pocket_len/2,0,0])
				cube(size=[pocket_len,m*2,nut_height],center=true);
			}
}

module HotendMount
(
	//mount base parameters
	center_hole_diam=4.6,
	side_hole_diam=3.2,
	side_hole1_pos=[-14,-3],
	side_hole2_pos=[19,-3],
	base_points=[[-18,-12],[24,-12],[24,11],[-18,11]],
	base_height=8,
	side_holes_nut_depth=3,
	//hotend block params
	hotend_block_size=[20.25,12.1,27],
	hotend_block_front=11,
	hotend_block_back=12,
	hotend_screws_diam=3.2,
	hotend_screws_diff=14,
	hotend_screws_z_shift=-4,
	hotend_screws_nut_depth=3,
	hotend_screws_cap_diam=7.5,
	hotend_screws_cap_depth=3.25,
	//hotend cooler params
	cooler_mount_screws_diff=29,
	cooler_mount_screws_z_shift=-4,
	cooler_mount_screws_diam=3.2,
	cooler_mount_screws_y_shift=2,
	cooler_nut_pocket_depth=3,
	cooler_nut_pocket_y_shift=6,
	//z probe mount params
	z_probe_screw_diam=3.2,
	z_probe_nut_pocket_depth=3,
	z_probe_screw_z_shift=-4,
	//fan params for extra front cut
	fan_size=[25.5,10.2,25.5],
	fan_air_hole_diam=24,
	quality=2,
)
{
	cutClr=0.1;
	difference()
	{
		//mount base
		translate([0,0,-base_height])
		linear_extrude(height=base_height)
		polygon(points=base_points);

		//central shaft
		translate([0,0,-base_height-cutClr])
		cylinder(d=center_hole_diam,h=base_height+2*cutClr,$fn=quality*12);

		//left mount hole
		translate([side_hole1_pos[0],side_hole1_pos[1],-base_height-cutClr])
		cylinder(d=side_hole_diam,h=base_height+2*cutClr,$fn=quality*12);

		translate([side_hole1_pos[0],side_hole1_pos[1],-base_height+side_holes_nut_depth])
		rotate(a=90,v=[0,0,1])
		rotate(a=180,v=[1,0,0])
		NutPocket(pocket_len=side_holes_nut_depth+cutClr);

		//right mount hole
		translate([side_hole2_pos[0],side_hole2_pos[1],-base_height-cutClr])
		cylinder(d=side_hole_diam,h=base_height+2*cutClr,$fn=quality*12);

		translate([side_hole2_pos[0],side_hole2_pos[1],-base_height+side_holes_nut_depth])
		rotate(a=90,v=[0,0,1])
		rotate(a=180,v=[1,0,0])
		NutPocket(pocket_len=side_holes_nut_depth+cutClr);

		//hotend block cut
		translate([-hotend_block_size[0]/2, -hotend_block_size[1]/2, -hotend_block_size[2]-cutClr])
		cube(size=[hotend_block_size[0],hotend_block_size[1],hotend_block_size[2]+2*cutClr],center=false);

		//hotend block screws
		for(i=[-1,1])
		{
			translate([i*hotend_screws_diff/2,-hotend_block_back,hotend_screws_z_shift])
			{
				rotate(a=-90,v=[1,0,0])
				cylinder(d=hotend_screws_diam,h=hotend_block_back+hotend_block_front,center=false,$fn=quality*12);

				translate([0,hotend_screws_nut_depth,0])
				rotate(a=90,v=[1,0,0])
				NutPocket(pocket_len=hotend_screws_nut_depth+cutClr);

				translate([0,hotend_block_back+hotend_block_front+cutClr,0])
				rotate(a=90,v=[1,0,0])
				cylinder(d=hotend_screws_cap_diam,h=hotend_screws_cap_depth+cutClr,center=false,$fn=quality*12);
			}
		}

		//cooler mount screws
		for(i=[-1,1])
		{
			translate([i*cooler_mount_screws_diff/2,cooler_mount_screws_y_shift,cooler_mount_screws_z_shift])
			rotate(a=-90,v=[1,0,0])
			cylinder(d=cooler_mount_screws_diam,h=hotend_block_front+cutClr,center=false,$fn=quality*12);

			translate([i*cooler_mount_screws_diff/2,cooler_nut_pocket_y_shift,cooler_mount_screws_z_shift])
			rotate(a=180,v=[1,0,0])
			VNutPocket(pocket_len=base_height,nut_height=cooler_nut_pocket_depth);
		}

		//z probe mount hole
		translate([0,0,z_probe_screw_z_shift])
		rotate(a=90,v=[1,0,0])
		cylinder(d=z_probe_screw_diam,h=hotend_block_back+cutClr,center=false,$fn=quality*12);
		//z probe mount pocket
		translate([0,-hotend_block_size[1]/2+cutClr,z_probe_screw_z_shift])
		rotate(a=90,v=[1,0,0])
		NutPocket(pocket_len=z_probe_nut_pocket_depth+cutClr);

		//front fan cut
		hull()
		{
			translate([0,hotend_block_front,-fan_size[2]/2])
			rotate(a=-90,v=[1,0,0])
			cylinder(d=fan_air_hole_diam,h=fan_size[1],center=false,$fn=quality*24);

			front_clip_len=hotend_block_front-hotend_block_size[1]/2;
			translate([-hotend_block_size[0]/2,hotend_block_front-front_clip_len,-base_height*2])
			cube(size=[hotend_block_size[0],front_clip_len,base_height], center=false);
		}
	}
}


HotendMount();

if($preview)
color([1,1,1,0.25])
render() EffectorMount(center_xy=true,center_z=true,rotate_motor=true);
