DarkCaster/3DPrintingStuff/Kossel_Vslot_2040/corner.scad

//include <MCAD/units/metric.scad>
include <../OpenSCAD_Modules/MCAD/stepper.scad>
use <../OpenSCAD_Modules/MCAD/boxes.scad>
use <../OpenSCAD_Modules/MCAD/polyholes.scad>

tslot_profile = 20;
tslot_width = 40;
tslot_thickness = 20;
tslot_slot_width = 5;

tslot_separation = 2;

min_wall_thickness = 5;

motor = Nema17;
motor_width = motorWidth (motor);
motor_screw_spacing = lookup (NemaDistanceBetweenMountingHoles, motor);

arm_length = 80;

base_inner_width = tslot_thickness + tslot_separation * 2;
clearance = 0.3;

$fs = 0.4;
$fa = 1;

module tslot_interface (slot_width, length, thickness = 1)
{
    translate ([-slot_width / 2, 0, 0])
    cube ([slot_width, length, thickness]);
}

module mirror_if (value, axis = X)
{
    if (value) {
        mirror (axis)
        children ();
    } else {
        children ();
    }
}

module trapezoid (u, d, h)
{
    polygon ([
            [-d/2, 0],
            [d/2, 0],
            [u/2, h],
            [-u/2, h]
        ]);
}

module equi_triangle (side, center = true)
{
    radius = side / 2 / sin (60);

    translate (center ? [0, 0, 0] : [-radius, 0, 0])
    circle (r = radius, $fn = 3);
}

module round (r)
{
    offset (r = r)
    offset (r = -r)
    children ();
}

module vertical_extrusion_shape (with_clearance = false)
{
    w = with_clearance ? tslot_thickness + clearance : tslot_thickness;
    h = with_clearance ? tslot_width + clearance : tslot_width;

    // poke hole for vertical extrusion
    translate ([-w / 2, 0])
    mirror (Y)
    square ([w, h]);
}

module horizontal_extrusion_shape ()
{
    place_horizontal_extrusion ()
    square ([tslot_thickness, arm_length]);
}

module place_horizontal_extrusion ()
{
    for (direction = [1, -1])
    mirror_if (direction < 0, X)
    translate ([base_inner_width / 2, 0])
    rotate (-30, Z)
    children ();
}

module corner_shape ()
{
    chord_length = (tslot_thickness / cos (30) * 2 +
        tslot_separation * 2 + tslot_thickness);
    triangle_y_offset = chord_length / 2 / tan (30);

    difference () {
        round (-5)
        union () {
            // truncated triangle
            difference () {
                translate ([0, -triangle_y_offset, 0])
                rotate (-90, Z)
                round (r = 20)
                equi_triangle (side = 200, center = false);

                // truncate the triangle
                translate ([-500, 0])
                square ([1000, 1000]);
            }

            // protrusion for extra tslot width
            offset (r = min_wall_thickness)
            translate ([-tslot_thickness / 2, -tslot_width])
            square ([tslot_thickness, tslot_width]);

            // arm length
            for (direction = [1, -1])
            translate ([direction * base_inner_width / 2, 0])
            rotate (-direction * 30, Z)
            translate ([direction * tslot_thickness, 0])
            mirror_if (direction > 0, X)
            square ([tslot_thickness + min_wall_thickness,
                    arm_length]);
        }
    }
}

module place_extrusion_screwholes ()
{
    // vertical extrusion
    for (i = [1/4, 3/4] * tslot_width)
    translate ([0, 0, i])
    {
        // outside facing holes
        rotate (-90, X)
        translate ([0, 0, -(tslot_width + min_wall_thickness + epsilon)])
        children ();

        // side holes
        for (i = [1, -1])
        mirror_if (i < 0, X)
        rotate (-90, Y)
        translate ([0, -30, -(tslot_thickness / 2 + min_wall_thickness)])
        children ();
    }

    // horizontal extrusion
    place_horizontal_extrusion ()
    for (y = [1/5, 3/4] * arm_length)
    for (tslot_pos = [10, 30])
    translate ([min_wall_thickness + epsilon, y, tslot_pos])
    rotate (-90, Y)
    children ();
}

module motor_cutout ()
{
    screw_spacing = motor_screw_spacing;

    for (x = [1, -1] * screw_spacing / 2)
    for (y = [1, -1] * screw_spacing / 2)
    translate ([x, y, -epsilon])
    polyhole (d = 3.3, h = min_wall_thickness + epsilon * 2);

    translate ([0, 0, -epsilon])
    polyhole (d = lookup (NemaRoundExtrusionDiameter, motor) + 0.3,
        h = min_wall_thickness + epsilon * 2);
}

module extrusion_cap_screw ()
{
    // screw hole
    translate ([0, 0, -epsilon])
    polyhole (d = 5.3,
        h = min_wall_thickness + tslot_thickness / 2);

    // cap screw head
    mirror (Z)
    polyhole (d = 8.53, h = 100);
}

module bottom_corner ()
{
    motor_plate_width = motor_width + min_wall_thickness * 6;
    motor_distance = max (
        (motor_plate_width - base_inner_width) / 2 * tan (60),
        lookup (NemaFrontAxleLength, Nema17) + 5
    );

    difference () {
        linear_extrude (height = tslot_width)
        difference () {
            round (-5)
            union () {
                corner_shape ();

                translate ([-motor_plate_width / 2,
                        -min_wall_thickness + motor_distance])
                square ([motor_plate_width, min_wall_thickness]);
            }

            vertical_extrusion_shape (with_clearance = true);
            horizontal_extrusion_shape ();
        }

        place_extrusion_screwholes ()
        extrusion_cap_screw ();

        translate ([0, motor_distance, -motor_width / 2 + tslot_width])
        rotate (90, X)
        motor_cutout ();
    }
}

module extrusions ()
{
    module single_bar ()
    cube ([tslot_thickness, 400, tslot_width]);

    place_horizontal_extrusion ()
    single_bar ();

    translate ([-10, 0, 0])
    rotate (90, X)
    single_bar ();
}

bottom_corner ();
%extrusions ();
