DarkCaster/3DPrintingStuff/Kossel_Vslot_2040/M5ToM3_PulleyInsert.scad

module Insert
(
	inner_diam=3.325,
	outer_diam=5.1,
	insert_height=8.5,
	base_height=1,
	base_diam=6,
	quality=2,
)
{
	cutClr=0.01;
	difference()
	{
		union()
		{
			translate([0,0,-cutClr])
			cylinder(d=outer_diam,h=insert_height+cutClr,$fn=quality*12);
			translate([0,0,-base_height])
			cylinder(d=base_diam,h=base_height,$fn=quality*12);
		}
		translate([0,0,-base_height-cutClr])
		cylinder(d=inner_diam,h=base_height+insert_height+2*cutClr,$fn=quality*12);
	}
}

module Spacer
(
	inner_diam=3.325,
	base_diam=6,
	spacer_height=4,
	quality=2,
)
{
	cutClr=0.01;
	difference()
	{
		cylinder(d=base_diam,h=spacer_height,$fn=quality*12);
		translate([0,0,-cutClr])
		cylinder(d=inner_diam,h=spacer_height+2*cutClr,$fn=quality*12);
	}
}

Insert();

translate([10,0])
Spacer();
