DarkCaster/3DPrintingStuff/OPIRouterCase1/assembly.scad

use <opi_zero_section.scad>
use <dub_e100_e1_section.scad>
use <psu-meanwell-rs15-5_section.scad>
use <top_section.scad>

//Section size: X;Y
Size=[110,66]; //[50:1:200]

//3D-pr. nozzle-size
Nozzle=0.4; //[0.1:0.1:0.8]

//3D-pr. Layer size
Layer=0.2; //[0.05:0.05:0.5]

//Target wall size
Wall=1.6; //[0.1:0.1:4]

//Target base size
Base=1; //[0.1:0.1:4]

//Screw diameter
Screw_Diam=4; //[1:0.1:5]

//Screw clearance (will be added to screw diameter)
Screw_Clearance=0.2; //[0.01:0.01:0.5]

//Vents size
Vent_Size=[10,2]; //[1:0.5:10]

//Vents period
Vent_Period=[15,4]; //[1:0.5:20]

//Vents angle
Vent_Angle=70; //[0:0.5:89]

//Rendering quality of round surfaces
Quality=2; //[1:1:10]

//Ext USB adapter layout
USB_Adapter_Layout=1; // [0:Forward, 1:Backward]

//Power plug
USE_Top_Plug=1; // [0:Side cable, 1:Top plug]

//Render target
Target=0; // [0:Assembly, 1:OrangePI Section, 2:DUB-E100 Section, 3:PSU Section, 4:Top cover]

FinalWallSz=ceil(Wall/Nozzle)>=2?ceil(Wall/Nozzle)*Nozzle:2*Nozzle;
echo("FinalWallSz:",FinalWallSz);

FinalBaseSz=ceil(Base/Layer)>=2?ceil(Base/Layer)*Layer:2*Layer;
echo("FinalBaseSz:",FinalBaseSz);

/* [Hidden] */

height1=0;
height2=opi_zero_section_height(base_sz=FinalBaseSz)+height1;
height3=dub_e100_section_height(base_sz=FinalBaseSz)+height2;
height4=psu_rs15_section_height(base_sz=FinalBaseSz)+height3;

total_sz=top_section_height(base_sz=FinalBaseSz)+height4;
echo("total_sz=",total_sz);

if(Target==0 || Target==1)
{
	translate([0,0,Target==0?height1:0])
		opi_zero_section(size=Size,
			wall_sz=FinalWallSz,
			base_sz=FinalBaseSz,
			screw_diam=Screw_Diam,
			screw_clearance=Screw_Clearance,
			vent_size=Vent_Size,
			vent_period=Vent_Period,
			vent_angle=Vent_Angle,
			center_xy=true);
}

if(Target==0 || Target==2)
{
	translate([0,0,Target==0?height2:0])
		dub_e100_section(size=Size,
			wall_sz=FinalWallSz,
			base_sz=FinalBaseSz,
			screw_diam=Screw_Diam,
			screw_clearance=Screw_Clearance,
			vent_size=Vent_Size,
			vent_period=Vent_Period,
			vent_angle=Vent_Angle,
			use_back_layout=USB_Adapter_Layout==1,
			center_xy=true);
}

if(Target==0 || Target==3)
{
	translate([0,0,Target==0?height3:0])
		psu_rs15_section(size=Size,
			wall_sz=FinalWallSz,
			base_sz=FinalBaseSz,
			screw_diam=Screw_Diam,
			screw_clearance=Screw_Clearance,
			vent_size=Vent_Size,
			vent_period=Vent_Period,
			vent_angle=Vent_Angle,
			top_plug=USE_Top_Plug==1,
			center_xy=true);
}

if(Target==0 || Target==4)
{
	translate([0,0,Target==0?height4:0])
		top_section(size=Size,
			wall_sz=FinalWallSz,
			base_sz=FinalBaseSz,
			screw_diam=Screw_Diam,
			screw_clearance=Screw_Clearance,
			top_plug=USE_Top_Plug==1,
			center_xy=true);
}
