DarkCaster/3DPrintingStuff/Other/m5.5x3.4mm_washer.scad

difference()
{
	cylinder(d=7.8,h=3.4,center=true,$fn=24*2);
	cylinder(d=5.5,h=3.4+0.2,center=true,$fn=24*2);
}
