DarkCaster/3DPrintingStuff/Other/m5x1.4mm_washer.scad

difference()
{
	cylinder(d=8,h=1.4,center=true,$fn=24*2);
	cylinder(d=5,h=1.4+0.2,center=true,$fn=24*2);
}
