DarkCaster/3DPrintingStuff/Other/m5x2mm_washer.scad

difference()
{
	cylinder(d=8,h=2,center=true,$fn=24*2);
	cylinder(d=5,h=2+0.2,center=true,$fn=24*2);
}
